METAL-ShanghaiTech/ViPSN/EUU/software/ESB_version/Receiver_for_EUU/project/config/sdk_config.h

/**
 * Copyright (c) 2017 - 2018, Nordic Semiconductor ASA
 *
 * All rights reserved.
 *
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
 * 3. Neither the name of Nordic Semiconductor ASA nor the names of its
 *    contributors may be used to endorse or promote products derived from this
 *    software without specific prior written permission.
 *
 * 4. This software, with or without modification, must only be used with a
 *    Nordic Semiconductor ASA integrated circuit.
 *
 * 5. Any software provided in binary form under this license must not be reverse
 *    engineered, decompiled, modified and/or disassembled.
 *
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
 */



#ifndef SDK_CONFIG_H
#define SDK_CONFIG_H
// <<< Use Configuration Wizard in Context Menu >>>\n
#ifdef USE_APP_CONFIG
#include "app_config.h"
#endif
// <h> nRF_Drivers 

//==========================================================
// <e> NRFX_PRS_ENABLED - nrfx_prs - Peripheral Resource Sharing module
//==========================================================
#ifndef NRFX_PRS_ENABLED
#define NRFX_PRS_ENABLED 1
#endif
// <q> NRFX_PRS_BOX_0_ENABLED  - Enables box 0 in the module.
 

#ifndef NRFX_PRS_BOX_0_ENABLED
#define NRFX_PRS_BOX_0_ENABLED 0
#endif

// <q> NRFX_PRS_BOX_1_ENABLED  - Enables box 1 in the module.
 

#ifndef NRFX_PRS_BOX_1_ENABLED
#define NRFX_PRS_BOX_1_ENABLED 0
#endif

// <q> NRFX_PRS_BOX_2_ENABLED  - Enables box 2 in the module.
 

#ifndef NRFX_PRS_BOX_2_ENABLED
#define NRFX_PRS_BOX_2_ENABLED 0
#endif

// <q> NRFX_PRS_BOX_3_ENABLED  - Enables box 3 in the module.
 

#ifndef NRFX_PRS_BOX_3_ENABLED
#define NRFX_PRS_BOX_3_ENABLED 0
#endif

// <q> NRFX_PRS_BOX_4_ENABLED  - Enables box 4 in the module.
 

#ifndef NRFX_PRS_BOX_4_ENABLED
#define NRFX_PRS_BOX_4_ENABLED 1
#endif

// <e> NRFX_PRS_CONFIG_LOG_ENABLED - Enables logging in the module.
//==========================================================
#ifndef NRFX_PRS_CONFIG_LOG_ENABLED
#define NRFX_PRS_CONFIG_LOG_ENABLED 0
#endif
// <o> NRFX_PRS_CONFIG_LOG_LEVEL  - Default Severity level
 
// <0=> Off 
// <1=> Error 
// <2=> Warning 
// <3=> Info 
// <4=> Debug 

#ifndef NRFX_PRS_CONFIG_LOG_LEVEL
#define NRFX_PRS_CONFIG_LOG_LEVEL 3
#endif

// <o> NRFX_PRS_CONFIG_INFO_COLOR  - ANSI escape code prefix.
 
// <0=> Default 
// <1=> Black 
// <2=> Red 
// <3=> Green 
// <4=> Yellow 
// <5=> Blue 
// <6=> Magenta 
// <7=> Cyan 
// <8=> White 

#ifndef NRFX_PRS_CONFIG_INFO_COLOR
#define NRFX_PRS_CONFIG_INFO_COLOR 0
#endif

// <o> NRFX_PRS_CONFIG_DEBUG_COLOR  - ANSI escape code prefix.
 
// <0=> Default 
// <1=> Black 
// <2=> Red 
// <3=> Green 
// <4=> Yellow 
// <5=> Blue 
// <6=> Magenta 
// <7=> Cyan 
// <8=> White 

#ifndef NRFX_PRS_CONFIG_DEBUG_COLOR
#define NRFX_PRS_CONFIG_DEBUG_COLOR 0
#endif

// </e>

// </e>

// <e> NRFX_UARTE_ENABLED - nrfx_uarte - UARTE peripheral driver
//==========================================================
#ifndef NRFX_UARTE_ENABLED
#define NRFX_UARTE_ENABLED 1
#endif
// <o> NRFX_UARTE0_ENABLED - Enable UARTE0 instance 
#ifndef NRFX_UARTE0_ENABLED
#define NRFX_UARTE0_ENABLED 0
#endif

// <o> NRFX_UARTE_DEFAULT_CONFIG_HWFC  - Hardware Flow Control
 
// <0=> Disabled 
// <1=> Enabled 

#ifndef NRFX_UARTE_DEFAULT_CONFIG_HWFC
#define NRFX_UARTE_DEFAULT_CONFIG_HWFC 0
#endif

// <o> NRFX_UARTE_DEFAULT_CONFIG_PARITY  - Parity
 
// <0=> Excluded 
// <14=> Included 

#ifndef NRFX_UARTE_DEFAULT_CONFIG_PARITY
#define NRFX_UARTE_DEFAULT_CONFIG_PARITY 0
#endif

// <o> NRFX_UARTE_DEFAULT_CONFIG_BAUDRATE  - Default Baudrate
 
// <323584=> 1200 baud 
// <643072=> 2400 baud 
// <1290240=> 4800 baud 
// <2576384=> 9600 baud 
// <3862528=> 14400 baud 
// <5152768=> 19200 baud 
// <7716864=> 28800 baud 
// <8388608=> 31250 baud 
// <10289152=> 38400 baud 
// <15007744=> 56000 baud 
// <15400960=> 57600 baud 
// <20615168=> 76800 baud 
// <30801920=> 115200 baud 
// <61865984=> 230400 baud 
// <67108864=> 250000 baud 
// <121634816=> 460800 baud 
// <251658240=> 921600 baud 
// <268435456=> 1000000 baud 

#ifndef NRFX_UARTE_DEFAULT_CONFIG_BAUDRATE
#define NRFX_UARTE_DEFAULT_CONFIG_BAUDRATE 30801920
#endif

// <o> NRFX_UARTE_DEFAULT_CONFIG_IRQ_PRIORITY  - Interrupt priority
 
// <0=> 0 (highest) 
// <1=> 1 
// <2=> 2 
// <3=> 3 
// <4=> 4 
// <5=> 5 
// <6=> 6 
// <7=> 7 

#ifndef NRFX_UARTE_DEFAULT_CONFIG_IRQ_PRIORITY
#define NRFX_UARTE_DEFAULT_CONFIG_IRQ_PRIORITY 6
#endif

// <e> NRFX_UARTE_CONFIG_LOG_ENABLED - Enables logging in the module.
//==========================================================
#ifndef NRFX_UARTE_CONFIG_LOG_ENABLED
#define NRFX_UARTE_CONFIG_LOG_ENABLED 0
#endif
// <o> NRFX_UARTE_CONFIG_LOG_LEVEL  - Default Severity level
 
// <0=> Off 
// <1=> Error 
// <2=> Warning 
// <3=> Info 
// <4=> Debug 

#ifndef NRFX_UARTE_CONFIG_LOG_LEVEL
#define NRFX_UARTE_CONFIG_LOG_LEVEL 3
#endif

// <o> NRFX_UARTE_CONFIG_INFO_COLOR  - ANSI escape code prefix.
 
// <0=> Default 
// <1=> Black 
// <2=> Red 
// <3=> Green 
// <4=> Yellow 
// <5=> Blue 
// <6=> Magenta 
// <7=> Cyan 
// <8=> White 

#ifndef NRFX_UARTE_CONFIG_INFO_COLOR
#define NRFX_UARTE_CONFIG_INFO_COLOR 0
#endif

// <o> NRFX_UARTE_CONFIG_DEBUG_COLOR  - ANSI escape code prefix.
 
// <0=> Default 
// <1=> Black 
// <2=> Red 
// <3=> Green 
// <4=> Yellow 
// <5=> Blue 
// <6=> Magenta 
// <7=> Cyan 
// <8=> White 

#ifndef NRFX_UARTE_CONFIG_DEBUG_COLOR
#define NRFX_UARTE_CONFIG_DEBUG_COLOR 0
#endif

// </e>

// </e>

// <e> NRFX_UART_ENABLED - nrfx_uart - UART peripheral driver
//==========================================================
#ifndef NRFX_UART_ENABLED
#define NRFX_UART_ENABLED 1
#endif
// <o> NRFX_UART0_ENABLED - Enable UART0 instance 
#ifndef NRFX_UART0_ENABLED
#define NRFX_UART0_ENABLED 0
#endif

// <o> NRFX_UART_DEFAULT_CONFIG_HWFC  - Hardware Flow Control
 
// <0=> Disabled 
// <1=> Enabled 

#ifndef NRFX_UART_DEFAULT_CONFIG_HWFC
#define NRFX_UART_DEFAULT_CONFIG_HWFC 0
#endif

// <o> NRFX_UART_DEFAULT_CONFIG_PARITY  - Parity
 
// <0=> Excluded 
// <14=> Included 

#ifndef NRFX_UART_DEFAULT_CONFIG_PARITY
#define NRFX_UART_DEFAULT_CONFIG_PARITY 0
#endif

// <o> NRFX_UART_DEFAULT_CONFIG_BAUDRATE  - Default Baudrate
 
// <323584=> 1200 baud 
// <643072=> 2400 baud 
// <1290240=> 4800 baud 
// <2576384=> 9600 baud 
// <3866624=> 14400 baud 
// <5152768=> 19200 baud 
// <7729152=> 28800 baud 
// <8388608=> 31250 baud 
// <10309632=> 38400 baud 
// <15007744=> 56000 baud 
// <15462400=> 57600 baud 
// <20615168=> 76800 baud 
// <30924800=> 115200 baud 
// <61845504=> 230400 baud 
// <67108864=> 250000 baud 
// <123695104=> 460800 baud 
// <247386112=> 921600 baud 
// <268435456=> 1000000 baud 

#ifndef NRFX_UART_DEFAULT_CONFIG_BAUDRATE
#define NRFX_UART_DEFAULT_CONFIG_BAUDRATE 30924800
#endif

// <o> NRFX_UART_DEFAULT_CONFIG_IRQ_PRIORITY  - Interrupt priority
 
// <0=> 0 (highest) 
// <1=> 1 
// <2=> 2 
// <3=> 3 
// <4=> 4 
// <5=> 5 
// <6=> 6 
// <7=> 7 

#ifndef NRFX_UART_DEFAULT_CONFIG_IRQ_PRIORITY
#define NRFX_UART_DEFAULT_CONFIG_IRQ_PRIORITY 6
#endif

// <e> NRFX_UART_CONFIG_LOG_ENABLED - Enables logging in the module.
//==========================================================
#ifndef NRFX_UART_CONFIG_LOG_ENABLED
#define NRFX_UART_CONFIG_LOG_ENABLED 0
#endif
// <o> NRFX_UART_CONFIG_LOG_LEVEL  - Default Severity level
 
// <0=> Off 
// <1=> Error 
// <2=> Warning 
// <3=> Info 
// <4=> Debug 

#ifndef NRFX_UART_CONFIG_LOG_LEVEL
#define NRFX_UART_CONFIG_LOG_LEVEL 3
#endif

// <o> NRFX_UART_CONFIG_INFO_COLOR  - ANSI escape code prefix.
 
// <0=> Default 
// <1=> Black 
// <2=> Red 
// <3=> Green 
// <4=> Yellow 
// <5=> Blue 
// <6=> Magenta 
// <7=> Cyan 
// <8=> White 

#ifndef NRFX_UART_CONFIG_INFO_COLOR
#define NRFX_UART_CONFIG_INFO_COLOR 0
#endif

// <o> NRFX_UART_CONFIG_DEBUG_COLOR  - ANSI escape code prefix.
 
// <0=> Default 
// <1=> Black 
// <2=> Red 
// <3=> Green 
// <4=> Yellow 
// <5=> Blue 
// <6=> Magenta 
// <7=> Cyan 
// <8=> White 

#ifndef NRFX_UART_CONFIG_DEBUG_COLOR
#define NRFX_UART_CONFIG_DEBUG_COLOR 0
#endif

// </e>

// </e>

// <e> UART_ENABLED - nrf_drv_uart - UART/UARTE peripheral driver - legacy layer
//==========================================================
#ifndef UART_ENABLED
#define UART_ENABLED 1
#endif
// <o> UART_DEFAULT_CONFIG_HWFC  - Hardware Flow Control
 
// <0=> Disabled 
// <1=> Enabled 

#ifndef UART_DEFAULT_CONFIG_HWFC
#define UART_DEFAULT_CONFIG_HWFC 0
#endif

// <o> UART_DEFAULT_CONFIG_PARITY  - Parity
 
// <0=> Excluded 
// <14=> Included 

#ifndef UART_DEFAULT_CONFIG_PARITY
#define UART_DEFAULT_CONFIG_PARITY 0
#endif

// <o> UART_DEFAULT_CONFIG_BAUDRATE  - Default Baudrate
 
// <323584=> 1200 baud 
// <643072=> 2400 baud 
// <1290240=> 4800 baud 
// <2576384=> 9600 baud 
// <3862528=> 14400 baud 
// <5152768=> 19200 baud 
// <7716864=> 28800 baud 
// <10289152=> 38400 baud 
// <15400960=> 57600 baud 
// <20615168=> 76800 baud 
// <30801920=> 115200 baud 
// <61865984=> 230400 baud 
// <67108864=> 250000 baud 
// <121634816=> 460800 baud 
// <251658240=> 921600 baud 
// <268435456=> 1000000 baud 

#ifndef UART_DEFAULT_CONFIG_BAUDRATE
#define UART_DEFAULT_CONFIG_BAUDRATE 30801920
#endif

// <o> UART_DEFAULT_CONFIG_IRQ_PRIORITY  - Interrupt priority
 

// <i> Priorities 0,2 (nRF51) and 0,1,4,5 (nRF52) are reserved for SoftDevice
// <0=> 0 (highest) 
// <1=> 1 
// <2=> 2 
// <3=> 3 
// <4=> 4 
// <5=> 5 
// <6=> 6 
// <7=> 7 

#ifndef UART_DEFAULT_CONFIG_IRQ_PRIORITY
#define UART_DEFAULT_CONFIG_IRQ_PRIORITY 6
#endif

// <q> UART_EASY_DMA_SUPPORT  - Driver supporting EasyDMA
 

#ifndef UART_EASY_DMA_SUPPORT
#define UART_EASY_DMA_SUPPORT 1
#endif

// <q> UART_LEGACY_SUPPORT  - Driver supporting Legacy mode
 

#ifndef UART_LEGACY_SUPPORT
#define UART_LEGACY_SUPPORT 1
#endif

// <e> UART0_ENABLED - Enable UART0 instance
//==========================================================
#ifndef UART0_ENABLED
#define UART0_ENABLED 1
#endif
// <q> UART0_CONFIG_USE_EASY_DMA  - Default setting for using EasyDMA
 

#ifndef UART0_CONFIG_USE_EASY_DMA
#define UART0_CONFIG_USE_EASY_DMA 1
#endif

// </e>

// </e>

// </h> 
//==========================================================
// <h> nRF_Libraries 
// <q> APP_FIFO_ENABLED  - app_fifo - Software FIFO implementation
 

#ifndef APP_FIFO_ENABLED
#define APP_FIFO_ENABLED 1
#endif

// <e> APP_UART_ENABLED - app_uart - UART driver
//==========================================================
#ifndef APP_UART_ENABLED
#define APP_UART_ENABLED 1
#endif
// <o> APP_UART_DRIVER_INSTANCE  - UART instance used
 
// <0=> 0 

#ifndef APP_UART_DRIVER_INSTANCE
#define APP_UART_DRIVER_INSTANCE 0
#endif

// </e>
//==========================================================
// <e> NRF_BALLOC_ENABLED - nrf_balloc - Block allocator module
//==========================================================
#ifndef NRF_BALLOC_ENABLED
#define NRF_BALLOC_ENABLED 1
#endif
// <e> NRF_BALLOC_CONFIG_DEBUG_ENABLED - Enables debug mode in the module.
//==========================================================
#ifndef NRF_BALLOC_CONFIG_DEBUG_ENABLED
#define NRF_BALLOC_CONFIG_DEBUG_ENABLED 0
#endif
// <o> NRF_BALLOC_CONFIG_HEAD_GUARD_WORDS - Number of words used as head guard.  <0-255> 


#ifndef NRF_BALLOC_CONFIG_HEAD_GUARD_WORDS
#define NRF_BALLOC_CONFIG_HEAD_GUARD_WORDS 1
#endif

// <o> NRF_BALLOC_CONFIG_TAIL_GUARD_WORDS - Number of words used as tail guard.  <0-255> 


#ifndef NRF_BALLOC_CONFIG_TAIL_GUARD_WORDS
#define NRF_BALLOC_CONFIG_TAIL_GUARD_WORDS 1
#endif

// <q> NRF_BALLOC_CONFIG_BASIC_CHECKS_ENABLED  - Enables basic checks in this module.
 

#ifndef NRF_BALLOC_CONFIG_BASIC_CHECKS_ENABLED
#define NRF_BALLOC_CONFIG_BASIC_CHECKS_ENABLED 0
#endif

// <q> NRF_BALLOC_CONFIG_DOUBLE_FREE_CHECK_ENABLED  - Enables double memory free check in this module.
 

#ifndef NRF_BALLOC_CONFIG_DOUBLE_FREE_CHECK_ENABLED
#define NRF_BALLOC_CONFIG_DOUBLE_FREE_CHECK_ENABLED 0
#endif

// <q> NRF_BALLOC_CONFIG_DATA_TRASHING_CHECK_ENABLED  - Enables free memory corruption check in this module.
 

#ifndef NRF_BALLOC_CONFIG_DATA_TRASHING_CHECK_ENABLED
#define NRF_BALLOC_CONFIG_DATA_TRASHING_CHECK_ENABLED 0
#endif

// <q> NRF_BALLOC_CLI_CMDS  - Enable CLI commands specific to the module
 

#ifndef NRF_BALLOC_CLI_CMDS
#define NRF_BALLOC_CLI_CMDS 0
#endif

// </e>

// </e>

// <q> NRF_FPRINTF_ENABLED  - nrf_fprintf - fprintf function.
 

#ifndef NRF_FPRINTF_ENABLED
#define NRF_FPRINTF_ENABLED 1
#endif

// <q> NRF_MEMOBJ_ENABLED  - nrf_memobj - Linked memory allocator module
 

#ifndef NRF_MEMOBJ_ENABLED
#define NRF_MEMOBJ_ENABLED 1
#endif

// <q> NRF_STRERROR_ENABLED  - nrf_strerror - Library for converting error code to string.
 

#ifndef NRF_STRERROR_ENABLED
#define NRF_STRERROR_ENABLED 1
#endif
// <q> RETARGET_ENABLED  - retarget - Retargeting stdio functions
 

#ifndef RETARGET_ENABLED
#define RETARGET_ENABLED 1
#endif


// </h> 
//==========================================================

// <h> nRF_Log 

//==========================================================
// <e> NRF_LOG_ENABLED - nrf_log - Logger
//==========================================================
#ifndef NRF_LOG_ENABLED
#define NRF_LOG_ENABLED 0
#endif
// <h> Log message pool - Configuration of log message pool

//==========================================================
// <o> NRF_LOG_MSGPOOL_ELEMENT_SIZE - Size of a single element in the pool of memory objects. 
// <i> If a small value is set, then performance of logs processing
// <i> is degraded because data is fragmented. Bigger value impacts
// <i> RAM memory utilization. The size is set to fit a message with
// <i> a timestamp and up to 2 arguments in a single memory object.

#ifndef NRF_LOG_MSGPOOL_ELEMENT_SIZE
#define NRF_LOG_MSGPOOL_ELEMENT_SIZE 20
#endif

// <o> NRF_LOG_MSGPOOL_ELEMENT_COUNT - Number of elements in the pool of memory objects 
// <i> If a small value is set, then it may lead to a deadlock
// <i> in certain cases if backend has high latency and holds
// <i> multiple messages for long time. Bigger value impacts
// <i> RAM memory usage.

#ifndef NRF_LOG_MSGPOOL_ELEMENT_COUNT
#define NRF_LOG_MSGPOOL_ELEMENT_COUNT 8
#endif

// </h> 
//==========================================================

// <q> NRF_LOG_ALLOW_OVERFLOW  - Configures behavior when circular buffer is full.
 

// <i> If set then oldest logs are overwritten. Otherwise a 
// <i> marker is injected informing about overflow.

#ifndef NRF_LOG_ALLOW_OVERFLOW
#define NRF_LOG_ALLOW_OVERFLOW 1
#endif

// <o> NRF_LOG_BUFSIZE  - Size of the buffer for storing logs (in bytes).
 

// <i> Must be power of 2 and multiple of 4.
// <i> If NRF_LOG_DEFERRED = 0 then buffer size can be reduced to minimum.
// <128=> 128 
// <256=> 256 
// <512=> 512 
// <1024=> 1024 
// <2048=> 2048 
// <4096=> 4096 
// <8192=> 8192 
// <16384=> 16384 

#ifndef NRF_LOG_BUFSIZE
#define NRF_LOG_BUFSIZE 1024
#endif

// <q> NRF_LOG_CLI_CMDS  - Enable CLI commands for the module.
 

#ifndef NRF_LOG_CLI_CMDS
#define NRF_LOG_CLI_CMDS 0
#endif

// <o> NRF_LOG_DEFAULT_LEVEL  - Default Severity level
 
// <0=> Off 
// <1=> Error 
// <2=> Warning 
// <3=> Info 
// <4=> Debug 

#ifndef NRF_LOG_DEFAULT_LEVEL
#define NRF_LOG_DEFAULT_LEVEL 3
#endif

// <q> NRF_LOG_DEFERRED  - Enable deffered logger.
 

// <i> Log data is buffered and can be processed in idle.

#ifndef NRF_LOG_DEFERRED
#define NRF_LOG_DEFERRED 1
#endif

// <q> NRF_LOG_FILTERS_ENABLED  - Enable dynamic filtering of logs.
 

#ifndef NRF_LOG_FILTERS_ENABLED
#define NRF_LOG_FILTERS_ENABLED 0
#endif

// <o> NRF_LOG_STR_PUSH_BUFFER_SIZE  - Size of the buffer dedicated for strings stored using @ref NRF_LOG_PUSH.
 
// <16=> 16 
// <32=> 32 
// <64=> 64 
// <128=> 128 
// <256=> 256 
// <512=> 512 
// <1024=> 1024 

#ifndef NRF_LOG_STR_PUSH_BUFFER_SIZE
#define NRF_LOG_STR_PUSH_BUFFER_SIZE 128
#endif

// <o> NRF_LOG_STR_PUSH_BUFFER_SIZE  - Size of the buffer dedicated for strings stored using @ref NRF_LOG_PUSH.
 
// <16=> 16 
// <32=> 32 
// <64=> 64 
// <128=> 128 
// <256=> 256 
// <512=> 512 
// <1024=> 1024 

#ifndef NRF_LOG_STR_PUSH_BUFFER_SIZE
#define NRF_LOG_STR_PUSH_BUFFER_SIZE 128
#endif

// <e> NRF_LOG_USES_COLORS - If enabled then ANSI escape code for colors is prefixed to every string
//==========================================================
#ifndef NRF_LOG_USES_COLORS
#define NRF_LOG_USES_COLORS 0
#endif
// <o> NRF_LOG_COLOR_DEFAULT  - ANSI escape code prefix.
 
// <0=> Default 
// <1=> Black 
// <2=> Red 
// <3=> Green 
// <4=> Yellow 
// <5=> Blue 
// <6=> Magenta 
// <7=> Cyan 
// <8=> White 

#ifndef NRF_LOG_COLOR_DEFAULT
#define NRF_LOG_COLOR_DEFAULT 0
#endif

// <o> NRF_LOG_ERROR_COLOR  - ANSI escape code prefix.
 
// <0=> Default 
// <1=> Black 
// <2=> Red 
// <3=> Green 
// <4=> Yellow 
// <5=> Blue 
// <6=> Magenta 
// <7=> Cyan 
// <8=> White 

#ifndef NRF_LOG_ERROR_COLOR
#define NRF_LOG_ERROR_COLOR 2
#endif

// <o> NRF_LOG_WARNING_COLOR  - ANSI escape code prefix.
 
// <0=> Default 
// <1=> Black 
// <2=> Red 
// <3=> Green 
// <4=> Yellow 
// <5=> Blue 
// <6=> Magenta 
// <7=> Cyan 
// <8=> White 

#ifndef NRF_LOG_WARNING_COLOR
#define NRF_LOG_WARNING_COLOR 4
#endif

// </e>

// <e> NRF_LOG_USES_TIMESTAMP - Enable timestamping

// <i> Function for getting the timestamp is provided by the user
//==========================================================
#ifndef NRF_LOG_USES_TIMESTAMP
#define NRF_LOG_USES_TIMESTAMP 0
#endif
// <o> NRF_LOG_TIMESTAMP_DEFAULT_FREQUENCY - Default frequency of the timestamp (in Hz) or 0 to use app_timer frequency. 
#ifndef NRF_LOG_TIMESTAMP_DEFAULT_FREQUENCY
#define NRF_LOG_TIMESTAMP_DEFAULT_FREQUENCY 0
#endif

// </e>

// <h> nrf_log module configuration 

//==========================================================
// <h> nrf_log in nRF_Core 

//==========================================================
// <e> NRF_MPU_CONFIG_LOG_ENABLED - Enables logging in the module.
//==========================================================
#ifndef NRF_MPU_CONFIG_LOG_ENABLED
#define NRF_MPU_CONFIG_LOG_ENABLED 0
#endif
// <o> NRF_MPU_CONFIG_LOG_LEVEL  - Default Severity level
 
// <0=> Off 
// <1=> Error 
// <2=> Warning 
// <3=> Info 
// <4=> Debug 

#ifndef NRF_MPU_CONFIG_LOG_LEVEL
#define NRF_MPU_CONFIG_LOG_LEVEL 3
#endif

// <o> NRF_MPU_CONFIG_INFO_COLOR  - ANSI escape code prefix.
 
// <0=> Default 
// <1=> Black 
// <2=> Red 
// <3=> Green 
// <4=> Yellow 
// <5=> Blue 
// <6=> Magenta 
// <7=> Cyan 
// <8=> White 

#ifndef NRF_MPU_CONFIG_INFO_COLOR
#define NRF_MPU_CONFIG_INFO_COLOR 0
#endif

// <o> NRF_MPU_CONFIG_DEBUG_COLOR  - ANSI escape code prefix.
 
// <0=> Default 
// <1=> Black 
// <2=> Red 
// <3=> Green 
// <4=> Yellow 
// <5=> Blue 
// <6=> Magenta 
// <7=> Cyan 
// <8=> White 

#ifndef NRF_MPU_CONFIG_DEBUG_COLOR
#define NRF_MPU_CONFIG_DEBUG_COLOR 0
#endif

// </e>

// <e> NRF_STACK_GUARD_CONFIG_LOG_ENABLED - Enables logging in the module.
//==========================================================
#ifndef NRF_STACK_GUARD_CONFIG_LOG_ENABLED
#define NRF_STACK_GUARD_CONFIG_LOG_ENABLED 0
#endif
// <o> NRF_STACK_GUARD_CONFIG_LOG_LEVEL  - Default Severity level
 
// <0=> Off 
// <1=> Error 
// <2=> Warning 
// <3=> Info 
// <4=> Debug 

#ifndef NRF_STACK_GUARD_CONFIG_LOG_LEVEL
#define NRF_STACK_GUARD_CONFIG_LOG_LEVEL 3
#endif

// <o> NRF_STACK_GUARD_CONFIG_INFO_COLOR  - ANSI escape code prefix.
 
// <0=> Default 
// <1=> Black 
// <2=> Red 
// <3=> Green 
// <4=> Yellow 
// <5=> Blue 
// <6=> Magenta 
// <7=> Cyan 
// <8=> White 

#ifndef NRF_STACK_GUARD_CONFIG_INFO_COLOR
#define NRF_STACK_GUARD_CONFIG_INFO_COLOR 0
#endif

// <o> NRF_STACK_GUARD_CONFIG_DEBUG_COLOR  - ANSI escape code prefix.
 
// <0=> Default 
// <1=> Black 
// <2=> Red 
// <3=> Green 
// <4=> Yellow 
// <5=> Blue 
// <6=> Magenta 
// <7=> Cyan 
// <8=> White 

#ifndef NRF_STACK_GUARD_CONFIG_DEBUG_COLOR
#define NRF_STACK_GUARD_CONFIG_DEBUG_COLOR 0
#endif

// </e>

// <e> TASK_MANAGER_CONFIG_LOG_ENABLED - Enables logging in the module.
//==========================================================
#ifndef TASK_MANAGER_CONFIG_LOG_ENABLED
#define TASK_MANAGER_CONFIG_LOG_ENABLED 0
#endif
// <o> TASK_MANAGER_CONFIG_LOG_LEVEL  - Default Severity level
 
// <0=> Off 
// <1=> Error 
// <2=> Warning 
// <3=> Info 
// <4=> Debug 

#ifndef TASK_MANAGER_CONFIG_LOG_LEVEL
#define TASK_MANAGER_CONFIG_LOG_LEVEL 3
#endif

// <o> TASK_MANAGER_CONFIG_INFO_COLOR  - ANSI escape code prefix.
 
// <0=> Default 
// <1=> Black 
// <2=> Red 
// <3=> Green 
// <4=> Yellow 
// <5=> Blue 
// <6=> Magenta 
// <7=> Cyan 
// <8=> White 

#ifndef TASK_MANAGER_CONFIG_INFO_COLOR
#define TASK_MANAGER_CONFIG_INFO_COLOR 0
#endif

// <o> TASK_MANAGER_CONFIG_DEBUG_COLOR  - ANSI escape code prefix.
 
// <0=> Default 
// <1=> Black 
// <2=> Red 
// <3=> Green 
// <4=> Yellow 
// <5=> Blue 
// <6=> Magenta 
// <7=> Cyan 
// <8=> White 

#ifndef TASK_MANAGER_CONFIG_DEBUG_COLOR
#define TASK_MANAGER_CONFIG_DEBUG_COLOR 0
#endif

// </e>

// </h> 
//==========================================================

// <h> nrf_log in nRF_Drivers 

//==========================================================
// <e> CLOCK_CONFIG_LOG_ENABLED - Enables logging in the module.
//==========================================================
#ifndef CLOCK_CONFIG_LOG_ENABLED
#define CLOCK_CONFIG_LOG_ENABLED 0
#endif
// <o> CLOCK_CONFIG_LOG_LEVEL  - Default Severity level
 
// <0=> Off 
// <1=> Error 
// <2=> Warning 
// <3=> Info 
// <4=> Debug 

#ifndef CLOCK_CONFIG_LOG_LEVEL
#define CLOCK_CONFIG_LOG_LEVEL 3
#endif

// <o> CLOCK_CONFIG_INFO_COLOR  - ANSI escape code prefix.
 
// <0=> Default 
// <1=> Black 
// <2=> Red 
// <3=> Green 
// <4=> Yellow 
// <5=> Blue 
// <6=> Magenta 
// <7=> Cyan 
// <8=> White 

#ifndef CLOCK_CONFIG_INFO_COLOR
#define CLOCK_CONFIG_INFO_COLOR 0
#endif

// <o> CLOCK_CONFIG_DEBUG_COLOR  - ANSI escape code prefix.
 
// <0=> Default 
// <1=> Black 
// <2=> Red 
// <3=> Green 
// <4=> Yellow 
// <5=> Blue 
// <6=> Magenta 
// <7=> Cyan 
// <8=> White 

#ifndef CLOCK_CONFIG_DEBUG_COLOR
#define CLOCK_CONFIG_DEBUG_COLOR 0
#endif

// </e>

// <e> COMP_CONFIG_LOG_ENABLED - Enables logging in the module.
//==========================================================
#ifndef COMP_CONFIG_LOG_ENABLED
#define COMP_CONFIG_LOG_ENABLED 0
#endif
// <o> COMP_CONFIG_LOG_LEVEL  - Default Severity level
 
// <0=> Off 
// <1=> Error 
// <2=> Warning 
// <3=> Info 
// <4=> Debug 

#ifndef COMP_CONFIG_LOG_LEVEL
#define COMP_CONFIG_LOG_LEVEL 3
#endif

// <o> COMP_CONFIG_INFO_COLOR  - ANSI escape code prefix.
 
// <0=> Default 
// <1=> Black 
// <2=> Red 
// <3=> Green 
// <4=> Yellow 
// <5=> Blue 
// <6=> Magenta 
// <7=> Cyan 
// <8=> White 

#ifndef COMP_CONFIG_INFO_COLOR
#define COMP_CONFIG_INFO_COLOR 0
#endif

// <o> COMP_CONFIG_DEBUG_COLOR  - ANSI escape code prefix.
 
// <0=> Default 
// <1=> Black 
// <2=> Red 
// <3=> Green 
// <4=> Yellow 
// <5=> Blue 
// <6=> Magenta 
// <7=> Cyan 
// <8=> White 

#ifndef COMP_CONFIG_DEBUG_COLOR
#define COMP_CONFIG_DEBUG_COLOR 0
#endif

// </e>

// <e> GPIOTE_CONFIG_LOG_ENABLED - Enables logging in the module.
//==========================================================
#ifndef GPIOTE_CONFIG_LOG_ENABLED
#define GPIOTE_CONFIG_LOG_ENABLED 0
#endif
// <o> GPIOTE_CONFIG_LOG_LEVEL  - Default Severity level
 
// <0=> Off 
// <1=> Error 
// <2=> Warning 
// <3=> Info 
// <4=> Debug 

#ifndef GPIOTE_CONFIG_LOG_LEVEL
#define GPIOTE_CONFIG_LOG_LEVEL 3
#endif

// <o> GPIOTE_CONFIG_INFO_COLOR  - ANSI escape code prefix.
 
// <0=> Default 
// <1=> Black 
// <2=> Red 
// <3=> Green 
// <4=> Yellow 
// <5=> Blue 
// <6=> Magenta 
// <7=> Cyan 
// <8=> White 

#ifndef GPIOTE_CONFIG_INFO_COLOR
#define GPIOTE_CONFIG_INFO_COLOR 0
#endif

// <o> GPIOTE_CONFIG_DEBUG_COLOR  - ANSI escape code prefix.
 
// <0=> Default 
// <1=> Black 
// <2=> Red 
// <3=> Green 
// <4=> Yellow 
// <5=> Blue 
// <6=> Magenta 
// <7=> Cyan 
// <8=> White 

#ifndef GPIOTE_CONFIG_DEBUG_COLOR
#define GPIOTE_CONFIG_DEBUG_COLOR 0
#endif

// </e>

// <e> LPCOMP_CONFIG_LOG_ENABLED - Enables logging in the module.
//==========================================================
#ifndef LPCOMP_CONFIG_LOG_ENABLED
#define LPCOMP_CONFIG_LOG_ENABLED 0
#endif
// <o> LPCOMP_CONFIG_LOG_LEVEL  - Default Severity level
 
// <0=> Off 
// <1=> Error 
// <2=> Warning 
// <3=> Info 
// <4=> Debug 

#ifndef LPCOMP_CONFIG_LOG_LEVEL
#define LPCOMP_CONFIG_LOG_LEVEL 3
#endif

// <o> LPCOMP_CONFIG_INFO_COLOR  - ANSI escape code prefix.
 
// <0=> Default 
// <1=> Black 
// <2=> Red 
// <3=> Green 
// <4=> Yellow 
// <5=> Blue 
// <6=> Magenta 
// <7=> Cyan 
// <8=> White 

#ifndef LPCOMP_CONFIG_INFO_COLOR
#define LPCOMP_CONFIG_INFO_COLOR 0
#endif

// <o> LPCOMP_CONFIG_DEBUG_COLOR  - ANSI escape code prefix.
 
// <0=> Default 
// <1=> Black 
// <2=> Red 
// <3=> Green 
// <4=> Yellow 
// <5=> Blue 
// <6=> Magenta 
// <7=> Cyan 
// <8=> White 

#ifndef LPCOMP_CONFIG_DEBUG_COLOR
#define LPCOMP_CONFIG_DEBUG_COLOR 0
#endif

// </e>

// <e> MAX3421E_HOST_CONFIG_LOG_ENABLED - Enable logging in the module
//==========================================================
#ifndef MAX3421E_HOST_CONFIG_LOG_ENABLED
#define MAX3421E_HOST_CONFIG_LOG_ENABLED 0
#endif
// <o> MAX3421E_HOST_CONFIG_LOG_LEVEL  - Default Severity level
 
// <0=> Off 
// <1=> Error 
// <2=> Warning 
// <3=> Info 
// <4=> Debug 

#ifndef MAX3421E_HOST_CONFIG_LOG_LEVEL
#define MAX3421E_HOST_CONFIG_LOG_LEVEL 3
#endif

// <o> MAX3421E_HOST_CONFIG_INFO_COLOR  - ANSI escape code prefix.
 
// <0=> Default 
// <1=> Black 
// <2=> Red 
// <3=> Green 
// <4=> Yellow 
// <5=> Blue 
// <6=> Magenta 
// <7=> Cyan 
// <8=> White 

#ifndef MAX3421E_HOST_CONFIG_INFO_COLOR
#define MAX3421E_HOST_CONFIG_INFO_COLOR 0
#endif

// <o> MAX3421E_HOST_CONFIG_DEBUG_COLOR  - ANSI escape code prefix.
 
// <0=> Default 
// <1=> Black 
// <2=> Red 
// <3=> Green 
// <4=> Yellow 
// <5=> Blue 
// <6=> Magenta 
// <7=> Cyan 
// <8=> White 

#ifndef MAX3421E_HOST_CONFIG_DEBUG_COLOR
#define MAX3421E_HOST_CONFIG_DEBUG_COLOR 0
#endif

// </e>

// <e> PDM_CONFIG_LOG_ENABLED - Enables logging in the module.
//==========================================================
#ifndef PDM_CONFIG_LOG_ENABLED
#define PDM_CONFIG_LOG_ENABLED 0
#endif
// <o> PDM_CONFIG_LOG_LEVEL  - Default Severity level
 
// <0=> Off 
// <1=> Error 
// <2=> Warning 
// <3=> Info 
// <4=> Debug 

#ifndef PDM_CONFIG_LOG_LEVEL
#define PDM_CONFIG_LOG_LEVEL 3
#endif

// <o> PDM_CONFIG_INFO_COLOR  - ANSI escape code prefix.
 
// <0=> Default 
// <1=> Black 
// <2=> Red 
// <3=> Green 
// <4=> Yellow 
// <5=> Blue 
// <6=> Magenta 
// <7=> Cyan 
// <8=> White 

#ifndef PDM_CONFIG_INFO_COLOR
#define PDM_CONFIG_INFO_COLOR 0
#endif

// <o> PDM_CONFIG_DEBUG_COLOR  - ANSI escape code prefix.
 
// <0=> Default 
// <1=> Black 
// <2=> Red 
// <3=> Green 
// <4=> Yellow 
// <5=> Blue 
// <6=> Magenta 
// <7=> Cyan 
// <8=> White 

#ifndef PDM_CONFIG_DEBUG_COLOR
#define PDM_CONFIG_DEBUG_COLOR 0
#endif

// </e>

// <e> PPI_CONFIG_LOG_ENABLED - Enables logging in the module.
//==========================================================
#ifndef PPI_CONFIG_LOG_ENABLED
#define PPI_CONFIG_LOG_ENABLED 0
#endif
// <o> PPI_CONFIG_LOG_LEVEL  - Default Severity level
 
// <0=> Off 
// <1=> Error 
// <2=> Warning 
// <3=> Info 
// <4=> Debug 

#ifndef PPI_CONFIG_LOG_LEVEL
#define PPI_CONFIG_LOG_LEVEL 3
#endif

// <o> PPI_CONFIG_INFO_COLOR  - ANSI escape code prefix.
 
// <0=> Default 
// <1=> Black 
// <2=> Red 
// <3=> Green 
// <4=> Yellow 
// <5=> Blue 
// <6=> Magenta 
// <7=> Cyan 
// <8=> White 

#ifndef PPI_CONFIG_INFO_COLOR
#define PPI_CONFIG_INFO_COLOR 0
#endif

// <o> PPI_CONFIG_DEBUG_COLOR  - ANSI escape code prefix.
 
// <0=> Default 
// <1=> Black 
// <2=> Red 
// <3=> Green 
// <4=> Yellow 
// <5=> Blue 
// <6=> Magenta 
// <7=> Cyan 
// <8=> White 

#ifndef PPI_CONFIG_DEBUG_COLOR
#define PPI_CONFIG_DEBUG_COLOR 0
#endif

// </e>

// <e> PWM_CONFIG_LOG_ENABLED - Enables logging in the module.
//==========================================================
#ifndef PWM_CONFIG_LOG_ENABLED
#define PWM_CONFIG_LOG_ENABLED 0
#endif
// <o> PWM_CONFIG_LOG_LEVEL  - Default Severity level
 
// <0=> Off 
// <1=> Error 
// <2=> Warning 
// <3=> Info 
// <4=> Debug 

#ifndef PWM_CONFIG_LOG_LEVEL
#define PWM_CONFIG_LOG_LEVEL 3
#endif

// <o> PWM_CONFIG_INFO_COLOR  - ANSI escape code prefix.
 
// <0=> Default 
// <1=> Black 
// <2=> Red 
// <3=> Green 
// <4=> Yellow 
// <5=> Blue 
// <6=> Magenta 
// <7=> Cyan 
// <8=> White 

#ifndef PWM_CONFIG_INFO_COLOR
#define PWM_CONFIG_INFO_COLOR 0
#endif

// <o> PWM_CONFIG_DEBUG_COLOR  - ANSI escape code prefix.
 
// <0=> Default 
// <1=> Black 
// <2=> Red 
// <3=> Green 
// <4=> Yellow 
// <5=> Blue 
// <6=> Magenta 
// <7=> Cyan 
// <8=> White 

#ifndef PWM_CONFIG_DEBUG_COLOR
#define PWM_CONFIG_DEBUG_COLOR 0
#endif

// </e>

// <e> QDEC_CONFIG_LOG_ENABLED - Enables logging in the module.
//==========================================================
#ifndef QDEC_CONFIG_LOG_ENABLED
#define QDEC_CONFIG_LOG_ENABLED 0
#endif
// <o> QDEC_CONFIG_LOG_LEVEL  - Default Severity level
 
// <0=> Off 
// <1=> Error 
// <2=> Warning 
// <3=> Info 
// <4=> Debug 

#ifndef QDEC_CONFIG_LOG_LEVEL
#define QDEC_CONFIG_LOG_LEVEL 3
#endif

// <o> QDEC_CONFIG_INFO_COLOR  - ANSI escape code prefix.
 
// <0=> Default 
// <1=> Black 
// <2=> Red 
// <3=> Green 
// <4=> Yellow 
// <5=> Blue 
// <6=> Magenta 
// <7=> Cyan 
// <8=> White 

#ifndef QDEC_CONFIG_INFO_COLOR
#define QDEC_CONFIG_INFO_COLOR 0
#endif

// <o> QDEC_CONFIG_DEBUG_COLOR  - ANSI escape code prefix.
 
// <0=> Default 
// <1=> Black 
// <2=> Red 
// <3=> Green 
// <4=> Yellow 
// <5=> Blue 
// <6=> Magenta 
// <7=> Cyan 
// <8=> White 

#ifndef QDEC_CONFIG_DEBUG_COLOR
#define QDEC_CONFIG_DEBUG_COLOR 0
#endif

// </e>

// <e> RNG_CONFIG_LOG_ENABLED - Enables logging in the module.
//==========================================================
#ifndef RNG_CONFIG_LOG_ENABLED
#define RNG_CONFIG_LOG_ENABLED 0
#endif
// <o> RNG_CONFIG_LOG_LEVEL  - Default Severity level
 
// <0=> Off 
// <1=> Error 
// <2=> Warning 
// <3=> Info 
// <4=> Debug 

#ifndef RNG_CONFIG_LOG_LEVEL
#define RNG_CONFIG_LOG_LEVEL 3
#endif

// <o> RNG_CONFIG_INFO_COLOR  - ANSI escape code prefix.
 
// <0=> Default 
// <1=> Black 
// <2=> Red 
// <3=> Green 
// <4=> Yellow 
// <5=> Blue 
// <6=> Magenta 
// <7=> Cyan 
// <8=> White 

#ifndef RNG_CONFIG_INFO_COLOR
#define RNG_CONFIG_INFO_COLOR 0
#endif

// <o> RNG_CONFIG_DEBUG_COLOR  - ANSI escape code prefix.
 
// <0=> Default 
// <1=> Black 
// <2=> Red 
// <3=> Green 
// <4=> Yellow 
// <5=> Blue 
// <6=> Magenta 
// <7=> Cyan 
// <8=> White 

#ifndef RNG_CONFIG_DEBUG_COLOR
#define RNG_CONFIG_DEBUG_COLOR 0
#endif

// <q> RNG_CONFIG_RANDOM_NUMBER_LOG_ENABLED  - Enables logging of random numbers.
 

#ifndef RNG_CONFIG_RANDOM_NUMBER_LOG_ENABLED
#define RNG_CONFIG_RANDOM_NUMBER_LOG_ENABLED 0
#endif

// </e>

// <e> RTC_CONFIG_LOG_ENABLED - Enables logging in the module.
//==========================================================
#ifndef RTC_CONFIG_LOG_ENABLED
#define RTC_CONFIG_LOG_ENABLED 0
#endif
// <o> RTC_CONFIG_LOG_LEVEL  - Default Severity level
 
// <0=> Off 
// <1=> Error 
// <2=> Warning 
// <3=> Info 
// <4=> Debug 

#ifndef RTC_CONFIG_LOG_LEVEL
#define RTC_CONFIG_LOG_LEVEL 3
#endif

// <o> RTC_CONFIG_INFO_COLOR  - ANSI escape code prefix.
 
// <0=> Default 
// <1=> Black 
// <2=> Red 
// <3=> Green 
// <4=> Yellow 
// <5=> Blue 
// <6=> Magenta 
// <7=> Cyan 
// <8=> White 

#ifndef RTC_CONFIG_INFO_COLOR
#define RTC_CONFIG_INFO_COLOR 0
#endif

// <o> RTC_CONFIG_DEBUG_COLOR  - ANSI escape code prefix.
 
// <0=> Default 
// <1=> Black 
// <2=> Red 
// <3=> Green 
// <4=> Yellow 
// <5=> Blue 
// <6=> Magenta 
// <7=> Cyan 
// <8=> White 

#ifndef RTC_CONFIG_DEBUG_COLOR
#define RTC_CONFIG_DEBUG_COLOR 0
#endif

// </e>

// <e> SAADC_CONFIG_LOG_ENABLED - Enables logging in the module.
//==========================================================
#ifndef SAADC_CONFIG_LOG_ENABLED
#define SAADC_CONFIG_LOG_ENABLED 0
#endif
// <o> SAADC_CONFIG_LOG_LEVEL  - Default Severity level
 
// <0=> Off 
// <1=> Error 
// <2=> Warning 
// <3=> Info 
// <4=> Debug 

#ifndef SAADC_CONFIG_LOG_LEVEL
#define SAADC_CONFIG_LOG_LEVEL 3
#endif

// <o> SAADC_CONFIG_INFO_COLOR  - ANSI escape code prefix.
 
// <0=> Default 
// <1=> Black 
// <2=> Red 
// <3=> Green 
// <4=> Yellow 
// <5=> Blue 
// <6=> Magenta 
// <7=> Cyan 
// <8=> White 

#ifndef SAADC_CONFIG_INFO_COLOR
#define SAADC_CONFIG_INFO_COLOR 0
#endif

// <o> SAADC_CONFIG_DEBUG_COLOR  - ANSI escape code prefix.
 
// <0=> Default 
// <1=> Black 
// <2=> Red 
// <3=> Green 
// <4=> Yellow 
// <5=> Blue 
// <6=> Magenta 
// <7=> Cyan 
// <8=> White 

#ifndef SAADC_CONFIG_DEBUG_COLOR
#define SAADC_CONFIG_DEBUG_COLOR 0
#endif

// </e>

// <e> SPIS_CONFIG_LOG_ENABLED - Enables logging in the module.
//==========================================================
#ifndef SPIS_CONFIG_LOG_ENABLED
#define SPIS_CONFIG_LOG_ENABLED 0
#endif
// <o> SPIS_CONFIG_LOG_LEVEL  - Default Severity level
 
// <0=> Off 
// <1=> Error 
// <2=> Warning 
// <3=> Info 
// <4=> Debug 

#ifndef SPIS_CONFIG_LOG_LEVEL
#define SPIS_CONFIG_LOG_LEVEL 3
#endif

// <o> SPIS_CONFIG_INFO_COLOR  - ANSI escape code prefix.
 
// <0=> Default 
// <1=> Black 
// <2=> Red 
// <3=> Green 
// <4=> Yellow 
// <5=> Blue 
// <6=> Magenta 
// <7=> Cyan 
// <8=> White 

#ifndef SPIS_CONFIG_INFO_COLOR
#define SPIS_CONFIG_INFO_COLOR 0
#endif

// <o> SPIS_CONFIG_DEBUG_COLOR  - ANSI escape code prefix.
 
// <0=> Default 
// <1=> Black 
// <2=> Red 
// <3=> Green 
// <4=> Yellow 
// <5=> Blue 
// <6=> Magenta 
// <7=> Cyan 
// <8=> White 

#ifndef SPIS_CONFIG_DEBUG_COLOR
#define SPIS_CONFIG_DEBUG_COLOR 0
#endif

// </e>

// <e> SPI_CONFIG_LOG_ENABLED - Enables logging in the module.
//==========================================================
#ifndef SPI_CONFIG_LOG_ENABLED
#define SPI_CONFIG_LOG_ENABLED 0
#endif
// <o> SPI_CONFIG_LOG_LEVEL  - Default Severity level
 
// <0=> Off 
// <1=> Error 
// <2=> Warning 
// <3=> Info 
// <4=> Debug 

#ifndef SPI_CONFIG_LOG_LEVEL
#define SPI_CONFIG_LOG_LEVEL 3
#endif

// <o> SPI_CONFIG_INFO_COLOR  - ANSI escape code prefix.
 
// <0=> Default 
// <1=> Black 
// <2=> Red 
// <3=> Green 
// <4=> Yellow 
// <5=> Blue 
// <6=> Magenta 
// <7=> Cyan 
// <8=> White 

#ifndef SPI_CONFIG_INFO_COLOR
#define SPI_CONFIG_INFO_COLOR 0
#endif

// <o> SPI_CONFIG_DEBUG_COLOR  - ANSI escape code prefix.
 
// <0=> Default 
// <1=> Black 
// <2=> Red 
// <3=> Green 
// <4=> Yellow 
// <5=> Blue 
// <6=> Magenta 
// <7=> Cyan 
// <8=> White 

#ifndef SPI_CONFIG_DEBUG_COLOR
#define SPI_CONFIG_DEBUG_COLOR 0
#endif

// </e>

// <e> TIMER_CONFIG_LOG_ENABLED - Enables logging in the module.
//==========================================================
#ifndef TIMER_CONFIG_LOG_ENABLED
#define TIMER_CONFIG_LOG_ENABLED 0
#endif
// <o> TIMER_CONFIG_LOG_LEVEL  - Default Severity level
 
// <0=> Off 
// <1=> Error 
// <2=> Warning 
// <3=> Info 
// <4=> Debug 

#ifndef TIMER_CONFIG_LOG_LEVEL
#define TIMER_CONFIG_LOG_LEVEL 3
#endif

// <o> TIMER_CONFIG_INFO_COLOR  - ANSI escape code prefix.
 
// <0=> Default 
// <1=> Black 
// <2=> Red 
// <3=> Green 
// <4=> Yellow 
// <5=> Blue 
// <6=> Magenta 
// <7=> Cyan 
// <8=> White 

#ifndef TIMER_CONFIG_INFO_COLOR
#define TIMER_CONFIG_INFO_COLOR 0
#endif

// <o> TIMER_CONFIG_DEBUG_COLOR  - ANSI escape code prefix.
 
// <0=> Default 
// <1=> Black 
// <2=> Red 
// <3=> Green 
// <4=> Yellow 
// <5=> Blue 
// <6=> Magenta 
// <7=> Cyan 
// <8=> White 

#ifndef TIMER_CONFIG_DEBUG_COLOR
#define TIMER_CONFIG_DEBUG_COLOR 0
#endif

// </e>

// <e> TWIS_CONFIG_LOG_ENABLED - Enables logging in the module.
//==========================================================
#ifndef TWIS_CONFIG_LOG_ENABLED
#define TWIS_CONFIG_LOG_ENABLED 0
#endif
// <o> TWIS_CONFIG_LOG_LEVEL  - Default Severity level
 
// <0=> Off 
// <1=> Error 
// <2=> Warning 
// <3=> Info 
// <4=> Debug 

#ifndef TWIS_CONFIG_LOG_LEVEL
#define TWIS_CONFIG_LOG_LEVEL 3
#endif

// <o> TWIS_CONFIG_INFO_COLOR  - ANSI escape code prefix.
 
// <0=> Default 
// <1=> Black 
// <2=> Red 
// <3=> Green 
// <4=> Yellow 
// <5=> Blue 
// <6=> Magenta 
// <7=> Cyan 
// <8=> White 

#ifndef TWIS_CONFIG_INFO_COLOR
#define TWIS_CONFIG_INFO_COLOR 0
#endif

// <o> TWIS_CONFIG_DEBUG_COLOR  - ANSI escape code prefix.
 
// <0=> Default 
// <1=> Black 
// <2=> Red 
// <3=> Green 
// <4=> Yellow 
// <5=> Blue 
// <6=> Magenta 
// <7=> Cyan 
// <8=> White 

#ifndef TWIS_CONFIG_DEBUG_COLOR
#define TWIS_CONFIG_DEBUG_COLOR 0
#endif

// </e>

// <e> TWI_CONFIG_LOG_ENABLED - Enables logging in the module.
//==========================================================
#ifndef TWI_CONFIG_LOG_ENABLED
#define TWI_CONFIG_LOG_ENABLED 0
#endif
// <o> TWI_CONFIG_LOG_LEVEL  - Default Severity level
 
// <0=> Off 
// <1=> Error 
// <2=> Warning 
// <3=> Info 
// <4=> Debug 

#ifndef TWI_CONFIG_LOG_LEVEL
#define TWI_CONFIG_LOG_LEVEL 3
#endif

// <o> TWI_CONFIG_INFO_COLOR  - ANSI escape code prefix.
 
// <0=> Default 
// <1=> Black 
// <2=> Red 
// <3=> Green 
// <4=> Yellow 
// <5=> Blue 
// <6=> Magenta 
// <7=> Cyan 
// <8=> White 

#ifndef TWI_CONFIG_INFO_COLOR
#define TWI_CONFIG_INFO_COLOR 0
#endif

// <o> TWI_CONFIG_DEBUG_COLOR  - ANSI escape code prefix.
 
// <0=> Default 
// <1=> Black 
// <2=> Red 
// <3=> Green 
// <4=> Yellow 
// <5=> Blue 
// <6=> Magenta 
// <7=> Cyan 
// <8=> White 

#ifndef TWI_CONFIG_DEBUG_COLOR
#define TWI_CONFIG_DEBUG_COLOR 0
#endif

// </e>

// <e> UART_CONFIG_LOG_ENABLED - Enables logging in the module.
//==========================================================
#ifndef UART_CONFIG_LOG_ENABLED
#define UART_CONFIG_LOG_ENABLED 0
#endif
// <o> UART_CONFIG_LOG_LEVEL  - Default Severity level
 
// <0=> Off 
// <1=> Error 
// <2=> Warning 
// <3=> Info 
// <4=> Debug 

#ifndef UART_CONFIG_LOG_LEVEL
#define UART_CONFIG_LOG_LEVEL 3
#endif

// <o> UART_CONFIG_INFO_COLOR  - ANSI escape code prefix.
 
// <0=> Default 
// <1=> Black 
// <2=> Red 
// <3=> Green 
// <4=> Yellow 
// <5=> Blue 
// <6=> Magenta 
// <7=> Cyan 
// <8=> White 

#ifndef UART_CONFIG_INFO_COLOR
#define UART_CONFIG_INFO_COLOR 0
#endif

// <o> UART_CONFIG_DEBUG_COLOR  - ANSI escape code prefix.
 
// <0=> Default 
// <1=> Black 
// <2=> Red 
// <3=> Green 
// <4=> Yellow 
// <5=> Blue 
// <6=> Magenta 
// <7=> Cyan 
// <8=> White 

#ifndef UART_CONFIG_DEBUG_COLOR
#define UART_CONFIG_DEBUG_COLOR 0
#endif

// </e>

// <e> USBD_CONFIG_LOG_ENABLED - Enable logging in the module
//==========================================================
#ifndef USBD_CONFIG_LOG_ENABLED
#define USBD_CONFIG_LOG_ENABLED 0
#endif
// <o> USBD_CONFIG_LOG_LEVEL  - Default Severity level
 
// <0=> Off 
// <1=> Error 
// <2=> Warning 
// <3=> Info 
// <4=> Debug 

#ifndef USBD_CONFIG_LOG_LEVEL
#define USBD_CONFIG_LOG_LEVEL 3
#endif

// <o> USBD_CONFIG_INFO_COLOR  - ANSI escape code prefix.
 
// <0=> Default 
// <1=> Black 
// <2=> Red 
// <3=> Green 
// <4=> Yellow 
// <5=> Blue 
// <6=> Magenta 
// <7=> Cyan 
// <8=> White 

#ifndef USBD_CONFIG_INFO_COLOR
#define USBD_CONFIG_INFO_COLOR 0
#endif

// <o> USBD_CONFIG_DEBUG_COLOR  - ANSI escape code prefix.
 
// <0=> Default 
// <1=> Black 
// <2=> Red 
// <3=> Green 
// <4=> Yellow 
// <5=> Blue 
// <6=> Magenta 
// <7=> Cyan 
// <8=> White 

#ifndef USBD_CONFIG_DEBUG_COLOR
#define USBD_CONFIG_DEBUG_COLOR 0
#endif

// </e>

// <e> WDT_CONFIG_LOG_ENABLED - Enables logging in the module.
//==========================================================
#ifndef WDT_CONFIG_LOG_ENABLED
#define WDT_CONFIG_LOG_ENABLED 0
#endif
// <o> WDT_CONFIG_LOG_LEVEL  - Default Severity level
 
// <0=> Off 
// <1=> Error 
// <2=> Warning 
// <3=> Info 
// <4=> Debug 

#ifndef WDT_CONFIG_LOG_LEVEL
#define WDT_CONFIG_LOG_LEVEL 3
#endif

// <o> WDT_CONFIG_INFO_COLOR  - ANSI escape code prefix.
 
// <0=> Default 
// <1=> Black 
// <2=> Red 
// <3=> Green 
// <4=> Yellow 
// <5=> Blue 
// <6=> Magenta 
// <7=> Cyan 
// <8=> White 

#ifndef WDT_CONFIG_INFO_COLOR
#define WDT_CONFIG_INFO_COLOR 0
#endif

// <o> WDT_CONFIG_DEBUG_COLOR  - ANSI escape code prefix.
 
// <0=> Default 
// <1=> Black 
// <2=> Red 
// <3=> Green 
// <4=> Yellow 
// <5=> Blue 
// <6=> Magenta 
// <7=> Cyan 
// <8=> White 

#ifndef WDT_CONFIG_DEBUG_COLOR
#define WDT_CONFIG_DEBUG_COLOR 0
#endif

// </e>

// </h> 
//==========================================================

// <h> nrf_log in nRF_Libraries 

//==========================================================
// <e> APP_TIMER_CONFIG_LOG_ENABLED - Enables logging in the module.
//==========================================================
#ifndef APP_TIMER_CONFIG_LOG_ENABLED
#define APP_TIMER_CONFIG_LOG_ENABLED 0
#endif
// <o> APP_TIMER_CONFIG_LOG_LEVEL  - Default Severity level
 
// <0=> Off 
// <1=> Error 
// <2=> Warning 
// <3=> Info 
// <4=> Debug 

#ifndef APP_TIMER_CONFIG_LOG_LEVEL
#define APP_TIMER_CONFIG_LOG_LEVEL 3
#endif

// <o> APP_TIMER_CONFIG_INITIAL_LOG_LEVEL  - Initial severity level if dynamic filtering is enabled.
 

// <i> If module generates a lot of logs, initial log level can
// <i> be decreased to prevent flooding. Severity level can be
// <i> increased on instance basis.
// <0=> Off 
// <1=> Error 
// <2=> Warning 
// <3=> Info 
// <4=> Debug 

#ifndef APP_TIMER_CONFIG_INITIAL_LOG_LEVEL
#define APP_TIMER_CONFIG_INITIAL_LOG_LEVEL 3
#endif

// <o> APP_TIMER_CONFIG_INFO_COLOR  - ANSI escape code prefix.
 
// <0=> Default 
// <1=> Black 
// <2=> Red 
// <3=> Green 
// <4=> Yellow 
// <5=> Blue 
// <6=> Magenta 
// <7=> Cyan 
// <8=> White 

#ifndef APP_TIMER_CONFIG_INFO_COLOR
#define APP_TIMER_CONFIG_INFO_COLOR 0
#endif

// <o> APP_TIMER_CONFIG_DEBUG_COLOR  - ANSI escape code prefix.
 
// <0=> Default 
// <1=> Black 
// <2=> Red 
// <3=> Green 
// <4=> Yellow 
// <5=> Blue 
// <6=> Magenta 
// <7=> Cyan 
// <8=> White 

#ifndef APP_TIMER_CONFIG_DEBUG_COLOR
#define APP_TIMER_CONFIG_DEBUG_COLOR 0
#endif

// </e>

// <e> APP_USBD_CDC_ACM_CONFIG_LOG_ENABLED - Enables logging in the module.
//==========================================================
#ifndef APP_USBD_CDC_ACM_CONFIG_LOG_ENABLED
#define APP_USBD_CDC_ACM_CONFIG_LOG_ENABLED 0
#endif
// <o> APP_USBD_CDC_ACM_CONFIG_LOG_LEVEL  - Default Severity level
 
// <0=> Off 
// <1=> Error 
// <2=> Warning 
// <3=> Info 
// <4=> Debug 

#ifndef APP_USBD_CDC_ACM_CONFIG_LOG_LEVEL
#define APP_USBD_CDC_ACM_CONFIG_LOG_LEVEL 3
#endif

// <o> APP_USBD_CDC_ACM_CONFIG_INFO_COLOR  - ANSI escape code prefix.
 
// <0=> Default 
// <1=> Black 
// <2=> Red 
// <3=> Green 
// <4=> Yellow 
// <5=> Blue 
// <6=> Magenta 
// <7=> Cyan 
// <8=> White 

#ifndef APP_USBD_CDC_ACM_CONFIG_INFO_COLOR
#define APP_USBD_CDC_ACM_CONFIG_INFO_COLOR 0
#endif

// <o> APP_USBD_CDC_ACM_CONFIG_DEBUG_COLOR  - ANSI escape code prefix.
 
// <0=> Default 
// <1=> Black 
// <2=> Red 
// <3=> Green 
// <4=> Yellow 
// <5=> Blue 
// <6=> Magenta 
// <7=> Cyan 
// <8=> White 

#ifndef APP_USBD_CDC_ACM_CONFIG_DEBUG_COLOR
#define APP_USBD_CDC_ACM_CONFIG_DEBUG_COLOR 0
#endif

// </e>

// <e> APP_USBD_CONFIG_LOG_ENABLED - Enable logging in the module.
//==========================================================
#ifndef APP_USBD_CONFIG_LOG_ENABLED
#define APP_USBD_CONFIG_LOG_ENABLED 0
#endif
// <o> APP_USBD_CONFIG_LOG_LEVEL  - Default Severity level
 
// <0=> Off 
// <1=> Error 
// <2=> Warning 
// <3=> Info 
// <4=> Debug 

#ifndef APP_USBD_CONFIG_LOG_LEVEL
#define APP_USBD_CONFIG_LOG_LEVEL 3
#endif

// <o> APP_USBD_CONFIG_INFO_COLOR  - ANSI escape code prefix.
 
// <0=> Default 
// <1=> Black 
// <2=> Red 
// <3=> Green 
// <4=> Yellow 
// <5=> Blue 
// <6=> Magenta 
// <7=> Cyan 
// <8=> White 

#ifndef APP_USBD_CONFIG_INFO_COLOR
#define APP_USBD_CONFIG_INFO_COLOR 0
#endif

// <o> APP_USBD_CONFIG_DEBUG_COLOR  - ANSI escape code prefix.
 
// <0=> Default 
// <1=> Black 
// <2=> Red 
// <3=> Green 
// <4=> Yellow 
// <5=> Blue 
// <6=> Magenta 
// <7=> Cyan 
// <8=> White 

#ifndef APP_USBD_CONFIG_DEBUG_COLOR
#define APP_USBD_CONFIG_DEBUG_COLOR 0
#endif

// </e>

// <e> APP_USBD_DUMMY_CONFIG_LOG_ENABLED - Enables logging in the module.
//==========================================================
#ifndef APP_USBD_DUMMY_CONFIG_LOG_ENABLED
#define APP_USBD_DUMMY_CONFIG_LOG_ENABLED 0
#endif
// <o> APP_USBD_DUMMY_CONFIG_LOG_LEVEL  - Default Severity level
 
// <0=> Off 
// <1=> Error 
// <2=> Warning 
// <3=> Info 
// <4=> Debug 

#ifndef APP_USBD_DUMMY_CONFIG_LOG_LEVEL
#define APP_USBD_DUMMY_CONFIG_LOG_LEVEL 3
#endif

// <o> APP_USBD_DUMMY_CONFIG_INFO_COLOR  - ANSI escape code prefix.
 
// <0=> Default 
// <1=> Black 
// <2=> Red 
// <3=> Green 
// <4=> Yellow 
// <5=> Blue 
// <6=> Magenta 
// <7=> Cyan 
// <8=> White 

#ifndef APP_USBD_DUMMY_CONFIG_INFO_COLOR
#define APP_USBD_DUMMY_CONFIG_INFO_COLOR 0
#endif

// <o> APP_USBD_DUMMY_CONFIG_DEBUG_COLOR  - ANSI escape code prefix.
 
// <0=> Default 
// <1=> Black 
// <2=> Red 
// <3=> Green 
// <4=> Yellow 
// <5=> Blue 
// <6=> Magenta 
// <7=> Cyan 
// <8=> White 

#ifndef APP_USBD_DUMMY_CONFIG_DEBUG_COLOR
#define APP_USBD_DUMMY_CONFIG_DEBUG_COLOR 0
#endif

// </e>

// <e> APP_USBD_MSC_CONFIG_LOG_ENABLED - Enables logging in the module.
//==========================================================
#ifndef APP_USBD_MSC_CONFIG_LOG_ENABLED
#define APP_USBD_MSC_CONFIG_LOG_ENABLED 0
#endif
// <o> APP_USBD_MSC_CONFIG_LOG_LEVEL  - Default Severity level
 
// <0=> Off 
// <1=> Error 
// <2=> Warning 
// <3=> Info 
// <4=> Debug 

#ifndef APP_USBD_MSC_CONFIG_LOG_LEVEL
#define APP_USBD_MSC_CONFIG_LOG_LEVEL 3
#endif

// <o> APP_USBD_MSC_CONFIG_INFO_COLOR  - ANSI escape code prefix.
 
// <0=> Default 
// <1=> Black 
// <2=> Red 
// <3=> Green 
// <4=> Yellow 
// <5=> Blue 
// <6=> Magenta 
// <7=> Cyan 
// <8=> White 

#ifndef APP_USBD_MSC_CONFIG_INFO_COLOR
#define APP_USBD_MSC_CONFIG_INFO_COLOR 0
#endif

// <o> APP_USBD_MSC_CONFIG_DEBUG_COLOR  - ANSI escape code prefix.
 
// <0=> Default 
// <1=> Black 
// <2=> Red 
// <3=> Green 
// <4=> Yellow 
// <5=> Blue 
// <6=> Magenta 
// <7=> Cyan 
// <8=> White 

#ifndef APP_USBD_MSC_CONFIG_DEBUG_COLOR
#define APP_USBD_MSC_CONFIG_DEBUG_COLOR 0
#endif

// </e>

// <e> APP_USBD_NRF_DFU_TRIGGER_CONFIG_LOG_ENABLED - Enables logging in the module.
//==========================================================
#ifndef APP_USBD_NRF_DFU_TRIGGER_CONFIG_LOG_ENABLED
#define APP_USBD_NRF_DFU_TRIGGER_CONFIG_LOG_ENABLED 0
#endif
// <o> APP_USBD_NRF_DFU_TRIGGER_CONFIG_LOG_LEVEL  - Default Severity level
 
// <0=> Off 
// <1=> Error 
// <2=> Warning 
// <3=> Info 
// <4=> Debug 

#ifndef APP_USBD_NRF_DFU_TRIGGER_CONFIG_LOG_LEVEL
#define APP_USBD_NRF_DFU_TRIGGER_CONFIG_LOG_LEVEL 3
#endif

// <o> APP_USBD_NRF_DFU_TRIGGER_CONFIG_INFO_COLOR  - ANSI escape code prefix.
 
// <0=> Default 
// <1=> Black 
// <2=> Red 
// <3=> Green 
// <4=> Yellow 
// <5=> Blue 
// <6=> Magenta 
// <7=> Cyan 
// <8=> White 

#ifndef APP_USBD_NRF_DFU_TRIGGER_CONFIG_INFO_COLOR
#define APP_USBD_NRF_DFU_TRIGGER_CONFIG_INFO_COLOR 0
#endif

// <o> APP_USBD_NRF_DFU_TRIGGER_CONFIG_DEBUG_COLOR  - ANSI escape code prefix.
 
// <0=> Default 
// <1=> Black 
// <2=> Red 
// <3=> Green 
// <4=> Yellow 
// <5=> Blue 
// <6=> Magenta 
// <7=> Cyan 
// <8=> White 

#ifndef APP_USBD_NRF_DFU_TRIGGER_CONFIG_DEBUG_COLOR
#define APP_USBD_NRF_DFU_TRIGGER_CONFIG_DEBUG_COLOR 0
#endif

// </e>

// <e> NRF_ATFIFO_CONFIG_LOG_ENABLED - Enables logging in the module.
//==========================================================
#ifndef NRF_ATFIFO_CONFIG_LOG_ENABLED
#define NRF_ATFIFO_CONFIG_LOG_ENABLED 0
#endif
// <o> NRF_ATFIFO_CONFIG_LOG_LEVEL  - Default Severity level
 
// <0=> Off 
// <1=> Error 
// <2=> Warning 
// <3=> Info 
// <4=> Debug 

#ifndef NRF_ATFIFO_CONFIG_LOG_LEVEL
#define NRF_ATFIFO_CONFIG_LOG_LEVEL 3
#endif

// <o> NRF_ATFIFO_CONFIG_LOG_INIT_FILTER_LEVEL  - Initial severity level if dynamic filtering is enabled
 
// <0=> Off 
// <1=> Error 
// <2=> Warning 
// <3=> Info 
// <4=> Debug 

#ifndef NRF_ATFIFO_CONFIG_LOG_INIT_FILTER_LEVEL
#define NRF_ATFIFO_CONFIG_LOG_INIT_FILTER_LEVEL 3
#endif

// <o> NRF_ATFIFO_CONFIG_INFO_COLOR  - ANSI escape code prefix.
 
// <0=> Default 
// <1=> Black 
// <2=> Red 
// <3=> Green 
// <4=> Yellow 
// <5=> Blue 
// <6=> Magenta 
// <7=> Cyan 
// <8=> White 

#ifndef NRF_ATFIFO_CONFIG_INFO_COLOR
#define NRF_ATFIFO_CONFIG_INFO_COLOR 0
#endif

// <o> NRF_ATFIFO_CONFIG_DEBUG_COLOR  - ANSI escape code prefix.
 
// <0=> Default 
// <1=> Black 
// <2=> Red 
// <3=> Green 
// <4=> Yellow 
// <5=> Blue 
// <6=> Magenta 
// <7=> Cyan 
// <8=> White 

#ifndef NRF_ATFIFO_CONFIG_DEBUG_COLOR
#define NRF_ATFIFO_CONFIG_DEBUG_COLOR 0
#endif

// </e>

// <e> NRF_BALLOC_CONFIG_LOG_ENABLED - Enables logging in the module.
//==========================================================
#ifndef NRF_BALLOC_CONFIG_LOG_ENABLED
#define NRF_BALLOC_CONFIG_LOG_ENABLED 0
#endif
// <o> NRF_BALLOC_CONFIG_LOG_LEVEL  - Default Severity level
 
// <0=> Off 
// <1=> Error 
// <2=> Warning 
// <3=> Info 
// <4=> Debug 

#ifndef NRF_BALLOC_CONFIG_LOG_LEVEL
#define NRF_BALLOC_CONFIG_LOG_LEVEL 3
#endif

// <o> NRF_BALLOC_CONFIG_INITIAL_LOG_LEVEL  - Initial severity level if dynamic filtering is enabled.
 

// <i> If module generates a lot of logs, initial log level can
// <i> be decreased to prevent flooding. Severity level can be
// <i> increased on instance basis.
// <0=> Off 
// <1=> Error 
// <2=> Warning 
// <3=> Info 
// <4=> Debug 

#ifndef NRF_BALLOC_CONFIG_INITIAL_LOG_LEVEL
#define NRF_BALLOC_CONFIG_INITIAL_LOG_LEVEL 3
#endif

// <o> NRF_BALLOC_CONFIG_INFO_COLOR  - ANSI escape code prefix.
 
// <0=> Default 
// <1=> Black 
// <2=> Red 
// <3=> Green 
// <4=> Yellow 
// <5=> Blue 
// <6=> Magenta 
// <7=> Cyan 
// <8=> White 

#ifndef NRF_BALLOC_CONFIG_INFO_COLOR
#define NRF_BALLOC_CONFIG_INFO_COLOR 0
#endif

// <o> NRF_BALLOC_CONFIG_DEBUG_COLOR  - ANSI escape code prefix.
 
// <0=> Default 
// <1=> Black 
// <2=> Red 
// <3=> Green 
// <4=> Yellow 
// <5=> Blue 
// <6=> Magenta 
// <7=> Cyan 
// <8=> White 

#ifndef NRF_BALLOC_CONFIG_DEBUG_COLOR
#define NRF_BALLOC_CONFIG_DEBUG_COLOR 0
#endif

// </e>

// <e> NRF_BLOCK_DEV_EMPTY_CONFIG_LOG_ENABLED - Enables logging in the module.
//==========================================================
#ifndef NRF_BLOCK_DEV_EMPTY_CONFIG_LOG_ENABLED
#define NRF_BLOCK_DEV_EMPTY_CONFIG_LOG_ENABLED 0
#endif
// <o> NRF_BLOCK_DEV_EMPTY_CONFIG_LOG_LEVEL  - Default Severity level
 
// <0=> Off 
// <1=> Error 
// <2=> Warning 
// <3=> Info 
// <4=> Debug 

#ifndef NRF_BLOCK_DEV_EMPTY_CONFIG_LOG_LEVEL
#define NRF_BLOCK_DEV_EMPTY_CONFIG_LOG_LEVEL 3
#endif

// <o> NRF_BLOCK_DEV_EMPTY_CONFIG_LOG_INIT_FILTER_LEVEL  - Initial severity level if dynamic filtering is enabled
 
// <0=> Off 
// <1=> Error 
// <2=> Warning 
// <3=> Info 
// <4=> Debug 

#ifndef NRF_BLOCK_DEV_EMPTY_CONFIG_LOG_INIT_FILTER_LEVEL
#define NRF_BLOCK_DEV_EMPTY_CONFIG_LOG_INIT_FILTER_LEVEL 3
#endif

// <o> NRF_BLOCK_DEV_EMPTY_CONFIG_INFO_COLOR  - ANSI escape code prefix.
 
// <0=> Default 
// <1=> Black 
// <2=> Red 
// <3=> Green 
// <4=> Yellow 
// <5=> Blue 
// <6=> Magenta 
// <7=> Cyan 
// <8=> White 

#ifndef NRF_BLOCK_DEV_EMPTY_CONFIG_INFO_COLOR
#define NRF_BLOCK_DEV_EMPTY_CONFIG_INFO_COLOR 0
#endif

// <o> NRF_BLOCK_DEV_EMPTY_CONFIG_DEBUG_COLOR  - ANSI escape code prefix.
 
// <0=> Default 
// <1=> Black 
// <2=> Red 
// <3=> Green 
// <4=> Yellow 
// <5=> Blue 
// <6=> Magenta 
// <7=> Cyan 
// <8=> White 

#ifndef NRF_BLOCK_DEV_EMPTY_CONFIG_DEBUG_COLOR
#define NRF_BLOCK_DEV_EMPTY_CONFIG_DEBUG_COLOR 0
#endif

// </e>

// <e> NRF_BLOCK_DEV_QSPI_CONFIG_LOG_ENABLED - Enables logging in the module.
//==========================================================
#ifndef NRF_BLOCK_DEV_QSPI_CONFIG_LOG_ENABLED
#define NRF_BLOCK_DEV_QSPI_CONFIG_LOG_ENABLED 0
#endif
// <o> NRF_BLOCK_DEV_QSPI_CONFIG_LOG_LEVEL  - Default Severity level
 
// <0=> Off 
// <1=> Error 
// <2=> Warning 
// <3=> Info 
// <4=> Debug 

#ifndef NRF_BLOCK_DEV_QSPI_CONFIG_LOG_LEVEL
#define NRF_BLOCK_DEV_QSPI_CONFIG_LOG_LEVEL 3
#endif

// <o> NRF_BLOCK_DEV_QSPI_CONFIG_LOG_INIT_FILTER_LEVEL  - Initial severity level if dynamic filtering is enabled
 
// <0=> Off 
// <1=> Error 
// <2=> Warning 
// <3=> Info 
// <4=> Debug 

#ifndef NRF_BLOCK_DEV_QSPI_CONFIG_LOG_INIT_FILTER_LEVEL
#define NRF_BLOCK_DEV_QSPI_CONFIG_LOG_INIT_FILTER_LEVEL 3
#endif

// <o> NRF_BLOCK_DEV_QSPI_CONFIG_INFO_COLOR  - ANSI escape code prefix.
 
// <0=> Default 
// <1=> Black 
// <2=> Red 
// <3=> Green 
// <4=> Yellow 
// <5=> Blue 
// <6=> Magenta 
// <7=> Cyan 
// <8=> White 

#ifndef NRF_BLOCK_DEV_QSPI_CONFIG_INFO_COLOR
#define NRF_BLOCK_DEV_QSPI_CONFIG_INFO_COLOR 0
#endif

// <o> NRF_BLOCK_DEV_QSPI_CONFIG_DEBUG_COLOR  - ANSI escape code prefix.
 
// <0=> Default 
// <1=> Black 
// <2=> Red 
// <3=> Green 
// <4=> Yellow 
// <5=> Blue 
// <6=> Magenta 
// <7=> Cyan 
// <8=> White 

#ifndef NRF_BLOCK_DEV_QSPI_CONFIG_DEBUG_COLOR
#define NRF_BLOCK_DEV_QSPI_CONFIG_DEBUG_COLOR 0
#endif

// </e>

// <e> NRF_BLOCK_DEV_RAM_CONFIG_LOG_ENABLED - Enables logging in the module.
//==========================================================
#ifndef NRF_BLOCK_DEV_RAM_CONFIG_LOG_ENABLED
#define NRF_BLOCK_DEV_RAM_CONFIG_LOG_ENABLED 0
#endif
// <o> NRF_BLOCK_DEV_RAM_CONFIG_LOG_LEVEL  - Default Severity level
 
// <0=> Off 
// <1=> Error 
// <2=> Warning 
// <3=> Info 
// <4=> Debug 

#ifndef NRF_BLOCK_DEV_RAM_CONFIG_LOG_LEVEL
#define NRF_BLOCK_DEV_RAM_CONFIG_LOG_LEVEL 3
#endif

// <o> NRF_BLOCK_DEV_RAM_CONFIG_LOG_INIT_FILTER_LEVEL  - Initial severity level if dynamic filtering is enabled
 
// <0=> Off 
// <1=> Error 
// <2=> Warning 
// <3=> Info 
// <4=> Debug 

#ifndef NRF_BLOCK_DEV_RAM_CONFIG_LOG_INIT_FILTER_LEVEL
#define NRF_BLOCK_DEV_RAM_CONFIG_LOG_INIT_FILTER_LEVEL 3
#endif

// <o> NRF_BLOCK_DEV_RAM_CONFIG_INFO_COLOR  - ANSI escape code prefix.
 
// <0=> Default 
// <1=> Black 
// <2=> Red 
// <3=> Green 
// <4=> Yellow 
// <5=> Blue 
// <6=> Magenta 
// <7=> Cyan 
// <8=> White 

#ifndef NRF_BLOCK_DEV_RAM_CONFIG_INFO_COLOR
#define NRF_BLOCK_DEV_RAM_CONFIG_INFO_COLOR 0
#endif

// <o> NRF_BLOCK_DEV_RAM_CONFIG_DEBUG_COLOR  - ANSI escape code prefix.
 
// <0=> Default 
// <1=> Black 
// <2=> Red 
// <3=> Green 
// <4=> Yellow 
// <5=> Blue 
// <6=> Magenta 
// <7=> Cyan 
// <8=> White 

#ifndef NRF_BLOCK_DEV_RAM_CONFIG_DEBUG_COLOR
#define NRF_BLOCK_DEV_RAM_CONFIG_DEBUG_COLOR 0
#endif

// </e>

// <e> NRF_CLI_BLE_UART_CONFIG_LOG_ENABLED - Enables logging in the module.
//==========================================================
#ifndef NRF_CLI_BLE_UART_CONFIG_LOG_ENABLED
#define NRF_CLI_BLE_UART_CONFIG_LOG_ENABLED 0
#endif
// <o> NRF_CLI_BLE_UART_CONFIG_LOG_LEVEL  - Default Severity level
 
// <0=> Off 
// <1=> Error 
// <2=> Warning 
// <3=> Info 
// <4=> Debug 

#ifndef NRF_CLI_BLE_UART_CONFIG_LOG_LEVEL
#define NRF_CLI_BLE_UART_CONFIG_LOG_LEVEL 3
#endif

// <o> NRF_CLI_BLE_UART_CONFIG_INFO_COLOR  - ANSI escape code prefix.
 
// <0=> Default 
// <1=> Black 
// <2=> Red 
// <3=> Green 
// <4=> Yellow 
// <5=> Blue 
// <6=> Magenta 
// <7=> Cyan 
// <8=> White 

#ifndef NRF_CLI_BLE_UART_CONFIG_INFO_COLOR
#define NRF_CLI_BLE_UART_CONFIG_INFO_COLOR 0
#endif

// <o> NRF_CLI_BLE_UART_CONFIG_DEBUG_COLOR  - ANSI escape code prefix.
 
// <0=> Default 
// <1=> Black 
// <2=> Red 
// <3=> Green 
// <4=> Yellow 
// <5=> Blue 
// <6=> Magenta 
// <7=> Cyan 
// <8=> White 

#ifndef NRF_CLI_BLE_UART_CONFIG_DEBUG_COLOR
#define NRF_CLI_BLE_UART_CONFIG_DEBUG_COLOR 0
#endif

// </e>

// <e> NRF_CLI_LIBUARTE_CONFIG_LOG_ENABLED - Enables logging in the module.
//==========================================================
#ifndef NRF_CLI_LIBUARTE_CONFIG_LOG_ENABLED
#define NRF_CLI_LIBUARTE_CONFIG_LOG_ENABLED 0
#endif
// <o> NRF_CLI_LIBUARTE_CONFIG_LOG_LEVEL  - Default Severity level
 
// <0=> Off 
// <1=> Error 
// <2=> Warning 
// <3=> Info 
// <4=> Debug 

#ifndef NRF_CLI_LIBUARTE_CONFIG_LOG_LEVEL
#define NRF_CLI_LIBUARTE_CONFIG_LOG_LEVEL 3
#endif

// <o> NRF_CLI_LIBUARTE_CONFIG_INFO_COLOR  - ANSI escape code prefix.
 
// <0=> Default 
// <1=> Black 
// <2=> Red 
// <3=> Green 
// <4=> Yellow 
// <5=> Blue 
// <6=> Magenta 
// <7=> Cyan 
// <8=> White 

#ifndef NRF_CLI_LIBUARTE_CONFIG_INFO_COLOR
#define NRF_CLI_LIBUARTE_CONFIG_INFO_COLOR 0
#endif

// <o> NRF_CLI_LIBUARTE_CONFIG_DEBUG_COLOR  - ANSI escape code prefix.
 
// <0=> Default 
// <1=> Black 
// <2=> Red 
// <3=> Green 
// <4=> Yellow 
// <5=> Blue 
// <6=> Magenta 
// <7=> Cyan 
// <8=> White 

#ifndef NRF_CLI_LIBUARTE_CONFIG_DEBUG_COLOR
#define NRF_CLI_LIBUARTE_CONFIG_DEBUG_COLOR 0
#endif

// </e>

// <e> NRF_CLI_UART_CONFIG_LOG_ENABLED - Enables logging in the module.
//==========================================================
#ifndef NRF_CLI_UART_CONFIG_LOG_ENABLED
#define NRF_CLI_UART_CONFIG_LOG_ENABLED 0
#endif
// <o> NRF_CLI_UART_CONFIG_LOG_LEVEL  - Default Severity level
 
// <0=> Off 
// <1=> Error 
// <2=> Warning 
// <3=> Info 
// <4=> Debug 

#ifndef NRF_CLI_UART_CONFIG_LOG_LEVEL
#define NRF_CLI_UART_CONFIG_LOG_LEVEL 3
#endif

// <o> NRF_CLI_UART_CONFIG_INFO_COLOR  - ANSI escape code prefix.
 
// <0=> Default 
// <1=> Black 
// <2=> Red 
// <3=> Green 
// <4=> Yellow 
// <5=> Blue 
// <6=> Magenta 
// <7=> Cyan 
// <8=> White 

#ifndef NRF_CLI_UART_CONFIG_INFO_COLOR
#define NRF_CLI_UART_CONFIG_INFO_COLOR 0
#endif

// <o> NRF_CLI_UART_CONFIG_DEBUG_COLOR  - ANSI escape code prefix.
 
// <0=> Default 
// <1=> Black 
// <2=> Red 
// <3=> Green 
// <4=> Yellow 
// <5=> Blue 
// <6=> Magenta 
// <7=> Cyan 
// <8=> White 

#ifndef NRF_CLI_UART_CONFIG_DEBUG_COLOR
#define NRF_CLI_UART_CONFIG_DEBUG_COLOR 0
#endif

// </e>

// <e> NRF_LIBUARTE_CONFIG_LOG_ENABLED - Enables logging in the module.
//==========================================================
#ifndef NRF_LIBUARTE_CONFIG_LOG_ENABLED
#define NRF_LIBUARTE_CONFIG_LOG_ENABLED 0
#endif
// <o> NRF_LIBUARTE_CONFIG_LOG_LEVEL  - Default Severity level
 
// <0=> Off 
// <1=> Error 
// <2=> Warning 
// <3=> Info 
// <4=> Debug 

#ifndef NRF_LIBUARTE_CONFIG_LOG_LEVEL
#define NRF_LIBUARTE_CONFIG_LOG_LEVEL 3
#endif

// <o> NRF_LIBUARTE_CONFIG_INFO_COLOR  - ANSI escape code prefix.
 
// <0=> Default 
// <1=> Black 
// <2=> Red 
// <3=> Green 
// <4=> Yellow 
// <5=> Blue 
// <6=> Magenta 
// <7=> Cyan 
// <8=> White 

#ifndef NRF_LIBUARTE_CONFIG_INFO_COLOR
#define NRF_LIBUARTE_CONFIG_INFO_COLOR 0
#endif

// <o> NRF_LIBUARTE_CONFIG_DEBUG_COLOR  - ANSI escape code prefix.
 
// <0=> Default 
// <1=> Black 
// <2=> Red 
// <3=> Green 
// <4=> Yellow 
// <5=> Blue 
// <6=> Magenta 
// <7=> Cyan 
// <8=> White 

#ifndef NRF_LIBUARTE_CONFIG_DEBUG_COLOR
#define NRF_LIBUARTE_CONFIG_DEBUG_COLOR 0
#endif

// </e>

// <e> NRF_MEMOBJ_CONFIG_LOG_ENABLED - Enables logging in the module.
//==========================================================
#ifndef NRF_MEMOBJ_CONFIG_LOG_ENABLED
#define NRF_MEMOBJ_CONFIG_LOG_ENABLED 0
#endif
// <o> NRF_MEMOBJ_CONFIG_LOG_LEVEL  - Default Severity level
 
// <0=> Off 
// <1=> Error 
// <2=> Warning 
// <3=> Info 
// <4=> Debug 

#ifndef NRF_MEMOBJ_CONFIG_LOG_LEVEL
#define NRF_MEMOBJ_CONFIG_LOG_LEVEL 3
#endif

// <o> NRF_MEMOBJ_CONFIG_INFO_COLOR  - ANSI escape code prefix.
 
// <0=> Default 
// <1=> Black 
// <2=> Red 
// <3=> Green 
// <4=> Yellow 
// <5=> Blue 
// <6=> Magenta 
// <7=> Cyan 
// <8=> White 

#ifndef NRF_MEMOBJ_CONFIG_INFO_COLOR
#define NRF_MEMOBJ_CONFIG_INFO_COLOR 0
#endif

// <o> NRF_MEMOBJ_CONFIG_DEBUG_COLOR  - ANSI escape code prefix.
 
// <0=> Default 
// <1=> Black 
// <2=> Red 
// <3=> Green 
// <4=> Yellow 
// <5=> Blue 
// <6=> Magenta 
// <7=> Cyan 
// <8=> White 

#ifndef NRF_MEMOBJ_CONFIG_DEBUG_COLOR
#define NRF_MEMOBJ_CONFIG_DEBUG_COLOR 0
#endif

// </e>

// <e> NRF_PWR_MGMT_CONFIG_LOG_ENABLED - Enables logging in the module.
//==========================================================
#ifndef NRF_PWR_MGMT_CONFIG_LOG_ENABLED
#define NRF_PWR_MGMT_CONFIG_LOG_ENABLED 0
#endif
// <o> NRF_PWR_MGMT_CONFIG_LOG_LEVEL  - Default Severity level
 
// <0=> Off 
// <1=> Error 
// <2=> Warning 
// <3=> Info 
// <4=> Debug 

#ifndef NRF_PWR_MGMT_CONFIG_LOG_LEVEL
#define NRF_PWR_MGMT_CONFIG_LOG_LEVEL 3
#endif

// <o> NRF_PWR_MGMT_CONFIG_INFO_COLOR  - ANSI escape code prefix.
 
// <0=> Default 
// <1=> Black 
// <2=> Red 
// <3=> Green 
// <4=> Yellow 
// <5=> Blue 
// <6=> Magenta 
// <7=> Cyan 
// <8=> White 

#ifndef NRF_PWR_MGMT_CONFIG_INFO_COLOR
#define NRF_PWR_MGMT_CONFIG_INFO_COLOR 0
#endif

// <o> NRF_PWR_MGMT_CONFIG_DEBUG_COLOR  - ANSI escape code prefix.
 
// <0=> Default 
// <1=> Black 
// <2=> Red 
// <3=> Green 
// <4=> Yellow 
// <5=> Blue 
// <6=> Magenta 
// <7=> Cyan 
// <8=> White 

#ifndef NRF_PWR_MGMT_CONFIG_DEBUG_COLOR
#define NRF_PWR_MGMT_CONFIG_DEBUG_COLOR 0
#endif

// </e>

// <e> NRF_QUEUE_CONFIG_LOG_ENABLED - Enables logging in the module.
//==========================================================
#ifndef NRF_QUEUE_CONFIG_LOG_ENABLED
#define NRF_QUEUE_CONFIG_LOG_ENABLED 0
#endif
// <o> NRF_QUEUE_CONFIG_LOG_LEVEL  - Default Severity level
 
// <0=> Off 
// <1=> Error 
// <2=> Warning 
// <3=> Info 
// <4=> Debug 

#ifndef NRF_QUEUE_CONFIG_LOG_LEVEL
#define NRF_QUEUE_CONFIG_LOG_LEVEL 3
#endif

// <o> NRF_QUEUE_CONFIG_LOG_INIT_FILTER_LEVEL  - Initial severity level if dynamic filtering is enabled
 
// <0=> Off 
// <1=> Error 
// <2=> Warning 
// <3=> Info 
// <4=> Debug 

#ifndef NRF_QUEUE_CONFIG_LOG_INIT_FILTER_LEVEL
#define NRF_QUEUE_CONFIG_LOG_INIT_FILTER_LEVEL 3
#endif

// <o> NRF_QUEUE_CONFIG_INFO_COLOR  - ANSI escape code prefix.
 
// <0=> Default 
// <1=> Black 
// <2=> Red 
// <3=> Green 
// <4=> Yellow 
// <5=> Blue 
// <6=> Magenta 
// <7=> Cyan 
// <8=> White 

#ifndef NRF_QUEUE_CONFIG_INFO_COLOR
#define NRF_QUEUE_CONFIG_INFO_COLOR 0
#endif

// <o> NRF_QUEUE_CONFIG_DEBUG_COLOR  - ANSI escape code prefix.
 
// <0=> Default 
// <1=> Black 
// <2=> Red 
// <3=> Green 
// <4=> Yellow 
// <5=> Blue 
// <6=> Magenta 
// <7=> Cyan 
// <8=> White 

#ifndef NRF_QUEUE_CONFIG_DEBUG_COLOR
#define NRF_QUEUE_CONFIG_DEBUG_COLOR 0
#endif

// </e>

// <e> NRF_SDH_ANT_LOG_ENABLED - Enable logging in SoftDevice handler (ANT) module.
//==========================================================
#ifndef NRF_SDH_ANT_LOG_ENABLED
#define NRF_SDH_ANT_LOG_ENABLED 0
#endif
// <o> NRF_SDH_ANT_LOG_LEVEL  - Default Severity level
 
// <0=> Off 
// <1=> Error 
// <2=> Warning 
// <3=> Info 
// <4=> Debug 

#ifndef NRF_SDH_ANT_LOG_LEVEL
#define NRF_SDH_ANT_LOG_LEVEL 3
#endif

// <o> NRF_SDH_ANT_INFO_COLOR  - ANSI escape code prefix.
 
// <0=> Default 
// <1=> Black 
// <2=> Red 
// <3=> Green 
// <4=> Yellow 
// <5=> Blue 
// <6=> Magenta 
// <7=> Cyan 
// <8=> White 

#ifndef NRF_SDH_ANT_INFO_COLOR
#define NRF_SDH_ANT_INFO_COLOR 0
#endif

// <o> NRF_SDH_ANT_DEBUG_COLOR  - ANSI escape code prefix.
 
// <0=> Default 
// <1=> Black 
// <2=> Red 
// <3=> Green 
// <4=> Yellow 
// <5=> Blue 
// <6=> Magenta 
// <7=> Cyan 
// <8=> White 

#ifndef NRF_SDH_ANT_DEBUG_COLOR
#define NRF_SDH_ANT_DEBUG_COLOR 0
#endif

// </e>

// <e> NRF_SDH_BLE_LOG_ENABLED - Enable logging in SoftDevice handler (BLE) module.
//==========================================================
#ifndef NRF_SDH_BLE_LOG_ENABLED
#define NRF_SDH_BLE_LOG_ENABLED 0
#endif
// <o> NRF_SDH_BLE_LOG_LEVEL  - Default Severity level
 
// <0=> Off 
// <1=> Error 
// <2=> Warning 
// <3=> Info 
// <4=> Debug 

#ifndef NRF_SDH_BLE_LOG_LEVEL
#define NRF_SDH_BLE_LOG_LEVEL 3
#endif

// <o> NRF_SDH_BLE_INFO_COLOR  - ANSI escape code prefix.
 
// <0=> Default 
// <1=> Black 
// <2=> Red 
// <3=> Green 
// <4=> Yellow 
// <5=> Blue 
// <6=> Magenta 
// <7=> Cyan 
// <8=> White 

#ifndef NRF_SDH_BLE_INFO_COLOR
#define NRF_SDH_BLE_INFO_COLOR 0
#endif

// <o> NRF_SDH_BLE_DEBUG_COLOR  - ANSI escape code prefix.
 
// <0=> Default 
// <1=> Black 
// <2=> Red 
// <3=> Green 
// <4=> Yellow 
// <5=> Blue 
// <6=> Magenta 
// <7=> Cyan 
// <8=> White 

#ifndef NRF_SDH_BLE_DEBUG_COLOR
#define NRF_SDH_BLE_DEBUG_COLOR 0
#endif

// </e>

// <e> NRF_SDH_LOG_ENABLED - Enable logging in SoftDevice handler module.
//==========================================================
#ifndef NRF_SDH_LOG_ENABLED
#define NRF_SDH_LOG_ENABLED 0
#endif
// <o> NRF_SDH_LOG_LEVEL  - Default Severity level
 
// <0=> Off 
// <1=> Error 
// <2=> Warning 
// <3=> Info 
// <4=> Debug 

#ifndef NRF_SDH_LOG_LEVEL
#define NRF_SDH_LOG_LEVEL 3
#endif

// <o> NRF_SDH_INFO_COLOR  - ANSI escape code prefix.
 
// <0=> Default 
// <1=> Black 
// <2=> Red 
// <3=> Green 
// <4=> Yellow 
// <5=> Blue 
// <6=> Magenta 
// <7=> Cyan 
// <8=> White 

#ifndef NRF_SDH_INFO_COLOR
#define NRF_SDH_INFO_COLOR 0
#endif

// <o> NRF_SDH_DEBUG_COLOR  - ANSI escape code prefix.
 
// <0=> Default 
// <1=> Black 
// <2=> Red 
// <3=> Green 
// <4=> Yellow 
// <5=> Blue 
// <6=> Magenta 
// <7=> Cyan 
// <8=> White 

#ifndef NRF_SDH_DEBUG_COLOR
#define NRF_SDH_DEBUG_COLOR 0
#endif

// </e>

// <e> NRF_SDH_SOC_LOG_ENABLED - Enable logging in SoftDevice handler (SoC) module.
//==========================================================
#ifndef NRF_SDH_SOC_LOG_ENABLED
#define NRF_SDH_SOC_LOG_ENABLED 0
#endif
// <o> NRF_SDH_SOC_LOG_LEVEL  - Default Severity level
 
// <0=> Off 
// <1=> Error 
// <2=> Warning 
// <3=> Info 
// <4=> Debug 

#ifndef NRF_SDH_SOC_LOG_LEVEL
#define NRF_SDH_SOC_LOG_LEVEL 3
#endif

// <o> NRF_SDH_SOC_INFO_COLOR  - ANSI escape code prefix.
 
// <0=> Default 
// <1=> Black 
// <2=> Red 
// <3=> Green 
// <4=> Yellow 
// <5=> Blue 
// <6=> Magenta 
// <7=> Cyan 
// <8=> White 

#ifndef NRF_SDH_SOC_INFO_COLOR
#define NRF_SDH_SOC_INFO_COLOR 0
#endif

// <o> NRF_SDH_SOC_DEBUG_COLOR  - ANSI escape code prefix.
 
// <0=> Default 
// <1=> Black 
// <2=> Red 
// <3=> Green 
// <4=> Yellow 
// <5=> Blue 
// <6=> Magenta 
// <7=> Cyan 
// <8=> White 

#ifndef NRF_SDH_SOC_DEBUG_COLOR
#define NRF_SDH_SOC_DEBUG_COLOR 0
#endif

// </e>

// <e> NRF_SORTLIST_CONFIG_LOG_ENABLED - Enables logging in the module.
//==========================================================
#ifndef NRF_SORTLIST_CONFIG_LOG_ENABLED
#define NRF_SORTLIST_CONFIG_LOG_ENABLED 0
#endif
// <o> NRF_SORTLIST_CONFIG_LOG_LEVEL  - Default Severity level
 
// <0=> Off 
// <1=> Error 
// <2=> Warning 
// <3=> Info 
// <4=> Debug 

#ifndef NRF_SORTLIST_CONFIG_LOG_LEVEL
#define NRF_SORTLIST_CONFIG_LOG_LEVEL 3
#endif

// <o> NRF_SORTLIST_CONFIG_INFO_COLOR  - ANSI escape code prefix.
 
// <0=> Default 
// <1=> Black 
// <2=> Red 
// <3=> Green 
// <4=> Yellow 
// <5=> Blue 
// <6=> Magenta 
// <7=> Cyan 
// <8=> White 

#ifndef NRF_SORTLIST_CONFIG_INFO_COLOR
#define NRF_SORTLIST_CONFIG_INFO_COLOR 0
#endif

// <o> NRF_SORTLIST_CONFIG_DEBUG_COLOR  - ANSI escape code prefix.
 
// <0=> Default 
// <1=> Black 
// <2=> Red 
// <3=> Green 
// <4=> Yellow 
// <5=> Blue 
// <6=> Magenta 
// <7=> Cyan 
// <8=> White 

#ifndef NRF_SORTLIST_CONFIG_DEBUG_COLOR
#define NRF_SORTLIST_CONFIG_DEBUG_COLOR 0
#endif

// </e>

// <e> NRF_TWI_SENSOR_CONFIG_LOG_ENABLED - Enables logging in the module.
//==========================================================
#ifndef NRF_TWI_SENSOR_CONFIG_LOG_ENABLED
#define NRF_TWI_SENSOR_CONFIG_LOG_ENABLED 0
#endif
// <o> NRF_TWI_SENSOR_CONFIG_LOG_LEVEL  - Default Severity level
 
// <0=> Off 
// <1=> Error 
// <2=> Warning 
// <3=> Info 
// <4=> Debug 

#ifndef NRF_TWI_SENSOR_CONFIG_LOG_LEVEL
#define NRF_TWI_SENSOR_CONFIG_LOG_LEVEL 3
#endif

// <o> NRF_TWI_SENSOR_CONFIG_INFO_COLOR  - ANSI escape code prefix.
 
// <0=> Default 
// <1=> Black 
// <2=> Red 
// <3=> Green 
// <4=> Yellow 
// <5=> Blue 
// <6=> Magenta 
// <7=> Cyan 
// <8=> White 

#ifndef NRF_TWI_SENSOR_CONFIG_INFO_COLOR
#define NRF_TWI_SENSOR_CONFIG_INFO_COLOR 0
#endif

// <o> NRF_TWI_SENSOR_CONFIG_DEBUG_COLOR  - ANSI escape code prefix.
 
// <0=> Default 
// <1=> Black 
// <2=> Red 
// <3=> Green 
// <4=> Yellow 
// <5=> Blue 
// <6=> Magenta 
// <7=> Cyan 
// <8=> White 

#ifndef NRF_TWI_SENSOR_CONFIG_DEBUG_COLOR
#define NRF_TWI_SENSOR_CONFIG_DEBUG_COLOR 0
#endif

// </e>

// <e> PM_LOG_ENABLED - Enable logging in Peer Manager and its submodules.
//==========================================================
#ifndef PM_LOG_ENABLED
#define PM_LOG_ENABLED 1
#endif
// <o> PM_LOG_LEVEL  - Default Severity level
 
// <0=> Off 
// <1=> Error 
// <2=> Warning 
// <3=> Info 
// <4=> Debug 

#ifndef PM_LOG_LEVEL
#define PM_LOG_LEVEL 3
#endif

// <o> PM_LOG_INFO_COLOR  - ANSI escape code prefix.
 
// <0=> Default 
// <1=> Black 
// <2=> Red 
// <3=> Green 
// <4=> Yellow 
// <5=> Blue 
// <6=> Magenta 
// <7=> Cyan 
// <8=> White 

#ifndef PM_LOG_INFO_COLOR
#define PM_LOG_INFO_COLOR 0
#endif

// <o> PM_LOG_DEBUG_COLOR  - ANSI escape code prefix.
 
// <0=> Default 
// <1=> Black 
// <2=> Red 
// <3=> Green 
// <4=> Yellow 
// <5=> Blue 
// <6=> Magenta 
// <7=> Cyan 
// <8=> White 

#ifndef PM_LOG_DEBUG_COLOR
#define PM_LOG_DEBUG_COLOR 0
#endif

// </e>

// </h> 
//==========================================================

// <h> nrf_log in nRF_Serialization 

//==========================================================
// <e> SER_HAL_TRANSPORT_CONFIG_LOG_ENABLED - Enables logging in the module.
//==========================================================
#ifndef SER_HAL_TRANSPORT_CONFIG_LOG_ENABLED
#define SER_HAL_TRANSPORT_CONFIG_LOG_ENABLED 0
#endif
// <o> SER_HAL_TRANSPORT_CONFIG_LOG_LEVEL  - Default Severity level
 
// <0=> Off 
// <1=> Error 
// <2=> Warning 
// <3=> Info 
// <4=> Debug 

#ifndef SER_HAL_TRANSPORT_CONFIG_LOG_LEVEL
#define SER_HAL_TRANSPORT_CONFIG_LOG_LEVEL 3
#endif

// <o> SER_HAL_TRANSPORT_CONFIG_INFO_COLOR  - ANSI escape code prefix.
 
// <0=> Default 
// <1=> Black 
// <2=> Red 
// <3=> Green 
// <4=> Yellow 
// <5=> Blue 
// <6=> Magenta 
// <7=> Cyan 
// <8=> White 

#ifndef SER_HAL_TRANSPORT_CONFIG_INFO_COLOR
#define SER_HAL_TRANSPORT_CONFIG_INFO_COLOR 0
#endif

// <o> SER_HAL_TRANSPORT_CONFIG_DEBUG_COLOR  - ANSI escape code prefix.
 
// <0=> Default 
// <1=> Black 
// <2=> Red 
// <3=> Green 
// <4=> Yellow 
// <5=> Blue 
// <6=> Magenta 
// <7=> Cyan 
// <8=> White 

#ifndef SER_HAL_TRANSPORT_CONFIG_DEBUG_COLOR
#define SER_HAL_TRANSPORT_CONFIG_DEBUG_COLOR 0
#endif

// </e>

// </h> 
//==========================================================

// </h> 
//==========================================================

// </e>

// <q> NRF_LOG_STR_FORMATTER_TIMESTAMP_FORMAT_ENABLED  - nrf_log_str_formatter - Log string formatter
 

#ifndef NRF_LOG_STR_FORMATTER_TIMESTAMP_FORMAT_ENABLED
#define NRF_LOG_STR_FORMATTER_TIMESTAMP_FORMAT_ENABLED 1
#endif

// </h> 
//==========================================================

// <<< end of configuration section >>>
#endif //SDK_CONFIG_H
